AS-Wilson/RogueGP/Documentation/Porfolio/Renders/140720 2.jpg

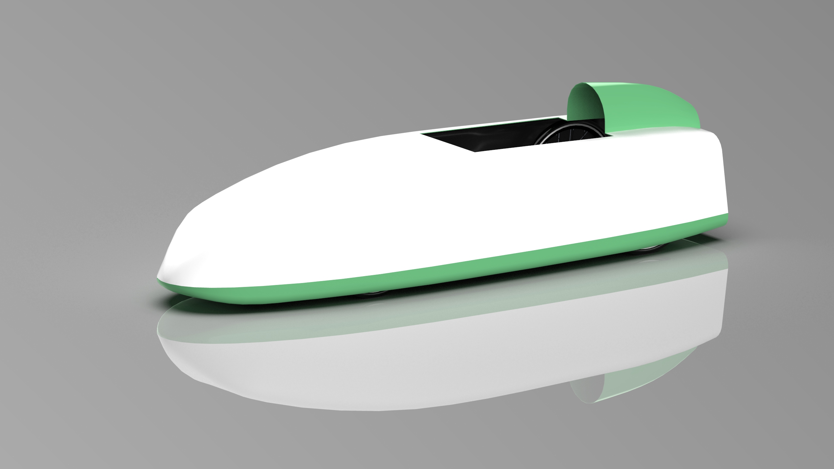
Documentation/Porfolio/Renders/140720 2.jpg
