AS-Wilson/RogueGP/Documentation/Porfolio/Renders/140720.jpg

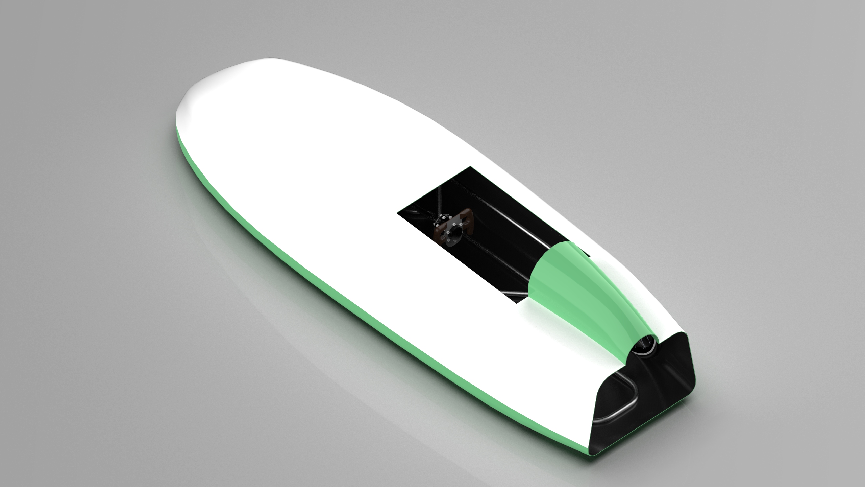
Documentation/Porfolio/Renders/140720.jpg
