AS-Wilson/RogueGP/Documentation/Porfolio/Renders/back.jpg

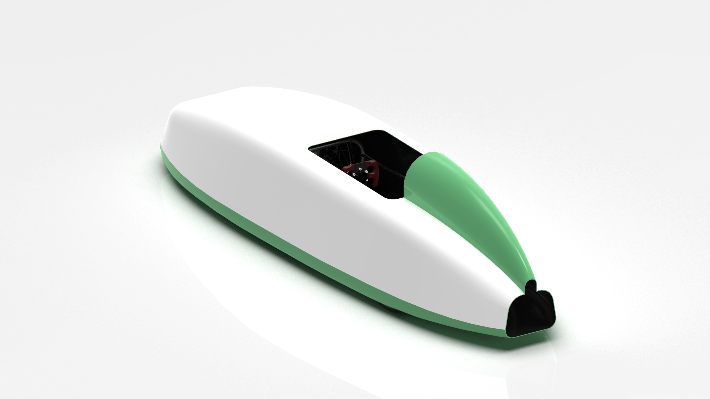
Documentation/Porfolio/Renders/back.jpg
