AS-Wilson/RogueGP/Documentation/Porfolio/Renders/Complete steering.jpg

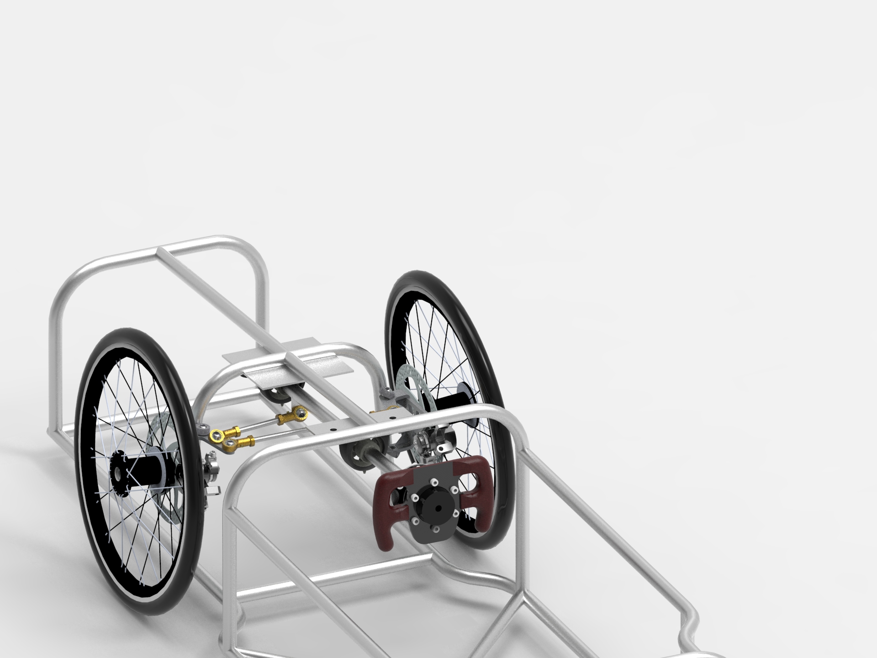
Documentation/Porfolio/Renders/Complete steering.jpg
