AS-Wilson/RogueGP/Documentation/Porfolio/Renders/Final Livery.jpg

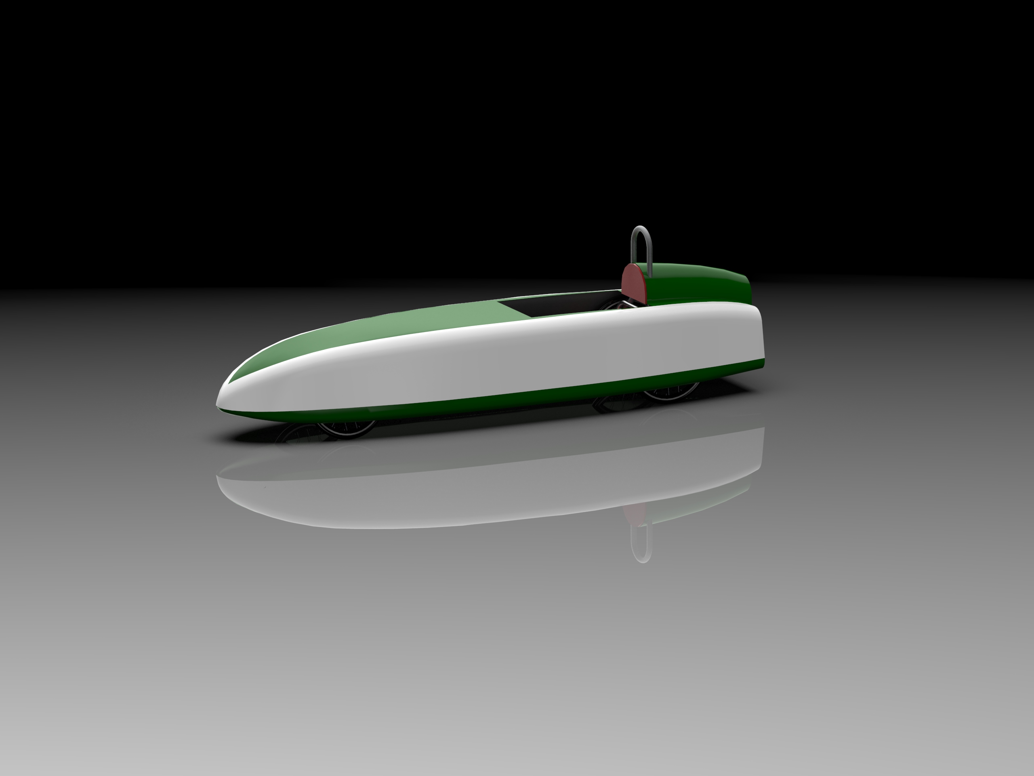
Documentation/Porfolio/Renders/Final Livery.jpg
