AS-Wilson/RogueGP/Documentation/Porfolio/Renders/front.jpg

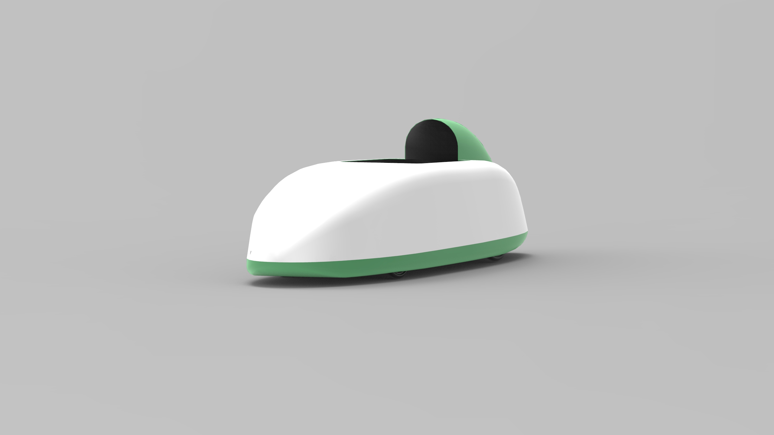
Documentation/Porfolio/Renders/front.jpg
