AS-Wilson/RogueGP/Documentation/Porfolio/Renders/Full Steering wheel 2.jpg

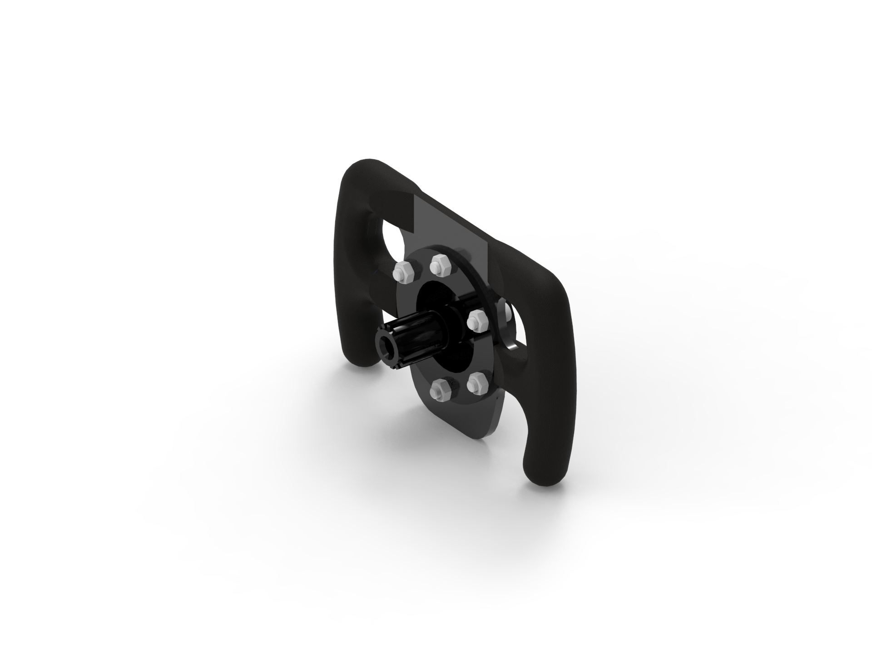
Documentation/Porfolio/Renders/Full Steering wheel 2.jpg
