AS-Wilson/RogueGP/Documentation/Porfolio/Renders/Full steering wheel.jpg

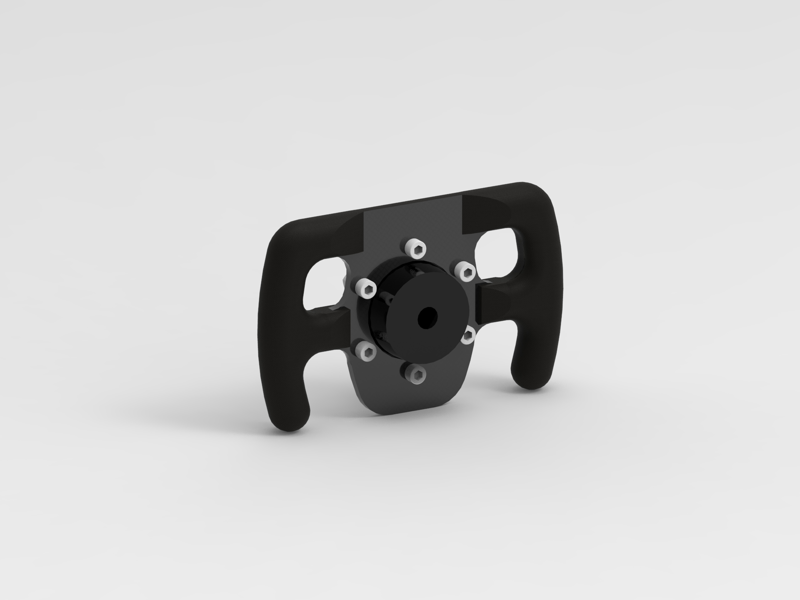
Documentation/Porfolio/Renders/Full steering wheel.jpg
