AS-Wilson/RogueGP/Documentation/Porfolio/Renders/KS®4539417097.115.jpg

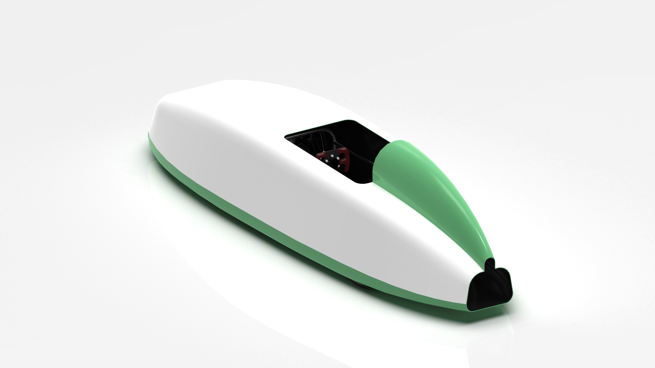
Documentation/Porfolio/Renders/KS®4539417097.115.jpg
