AS-Wilson/RogueGP/Documentation/Porfolio/Renders/Livery 1.jpg

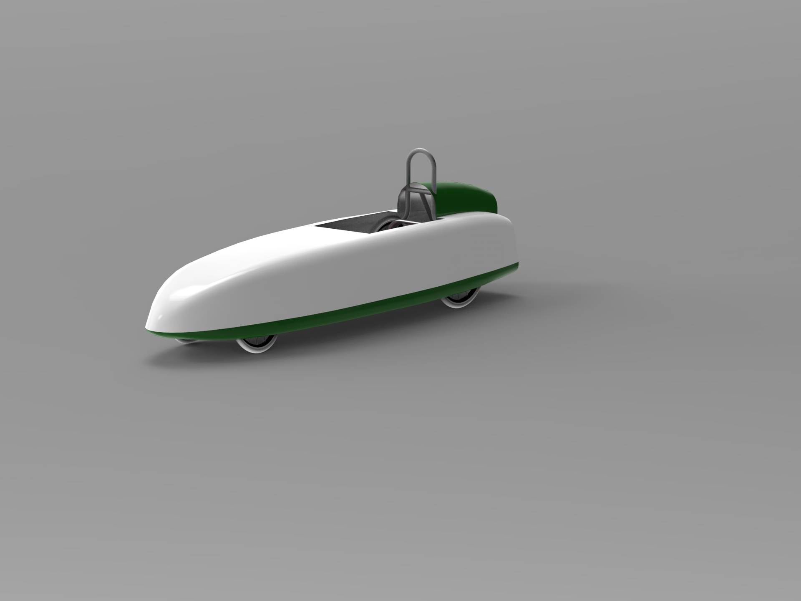
Documentation/Porfolio/Renders/Livery 1.jpg
