AS-Wilson/RogueGP/Documentation/Porfolio/Renders/Livery 1b.jpg

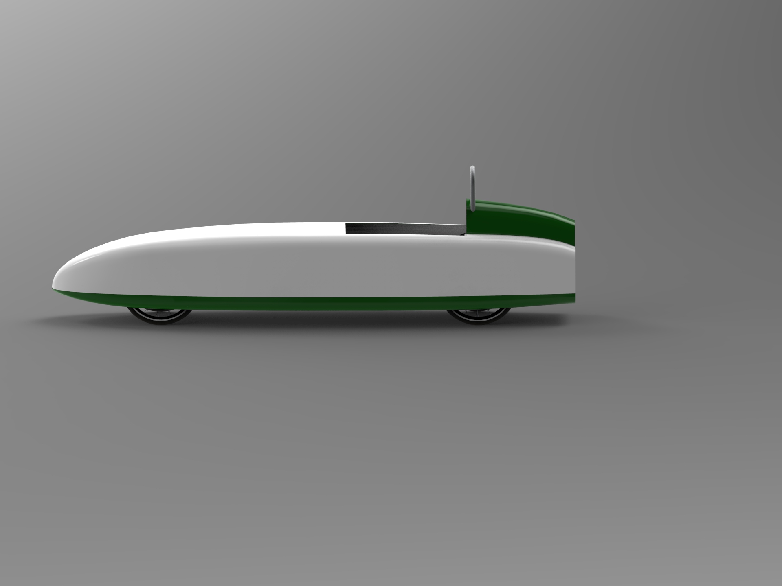
Documentation/Porfolio/Renders/Livery 1b.jpg
