AS-Wilson/RogueGP/Documentation/Porfolio/Renders/Livery 2.jpg

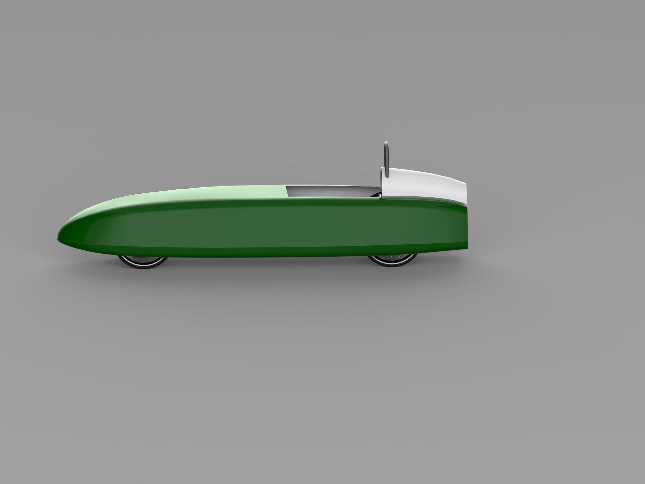
Documentation/Porfolio/Renders/Livery 2.jpg
