AS-Wilson/RogueGP/Documentation/Porfolio/Renders/Livery 3.jpg

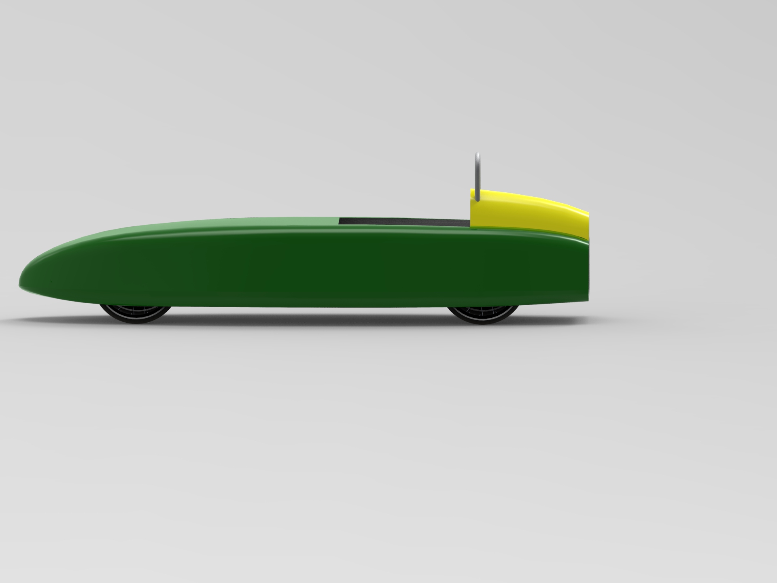
Documentation/Porfolio/Renders/Livery 3.jpg
