AS-Wilson/RogueGP/Documentation/Porfolio/Renders/Livery 4.jpg

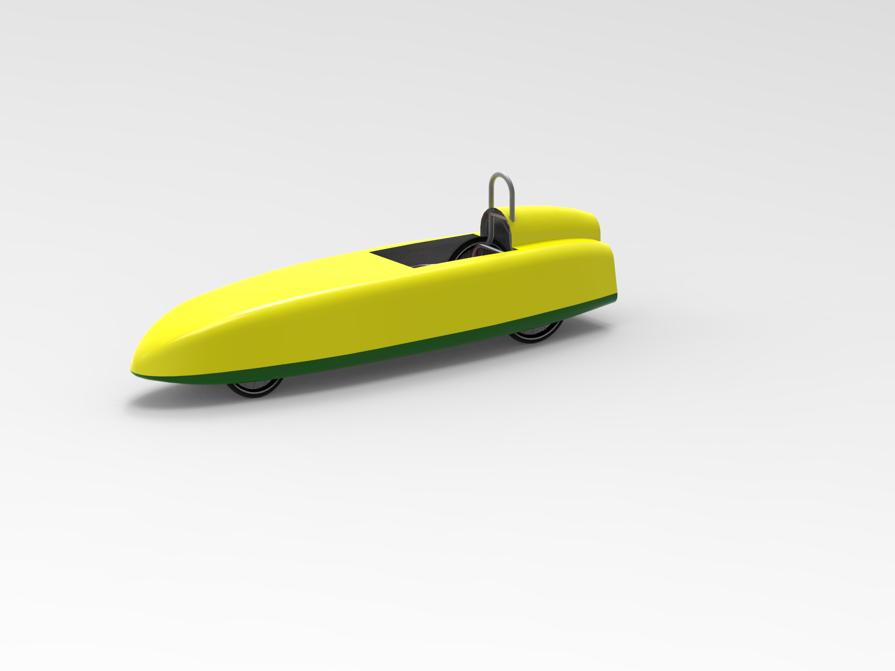
Documentation/Porfolio/Renders/Livery 4.jpg
