AS-Wilson/RogueGP/Documentation/Porfolio/Renders/Livery 5.jpg

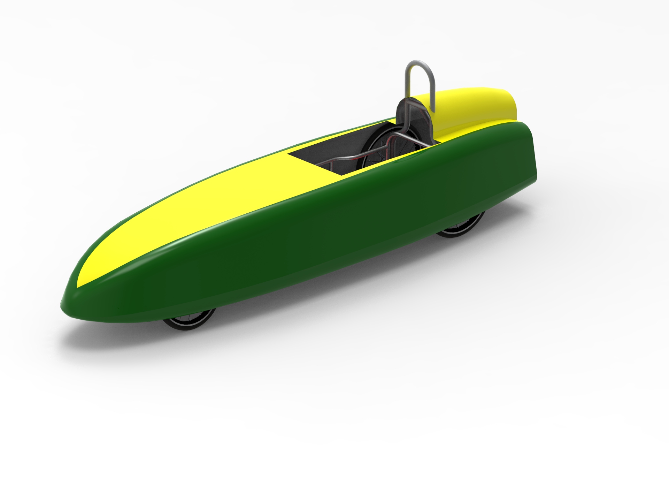
Documentation/Porfolio/Renders/Livery 5.jpg
