AS-Wilson/RogueGP/Documentation/Porfolio/Renders/Livery 6.jpg

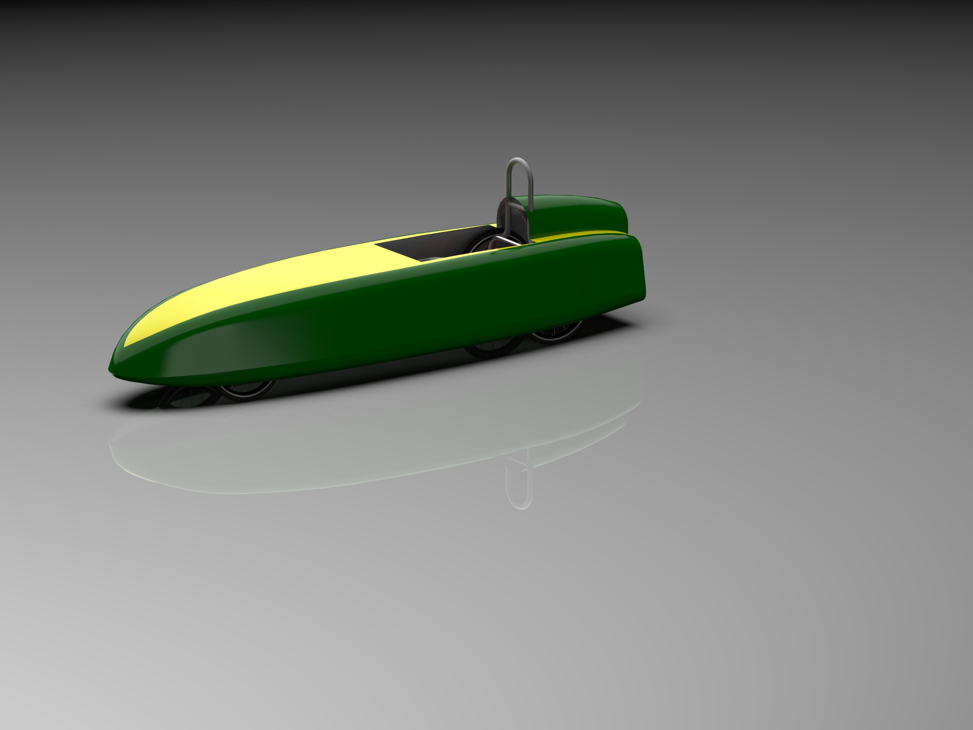
Documentation/Porfolio/Renders/Livery 6.jpg
