AS-Wilson/RogueGP/Documentation/Porfolio/Renders/Livery 7.jpg

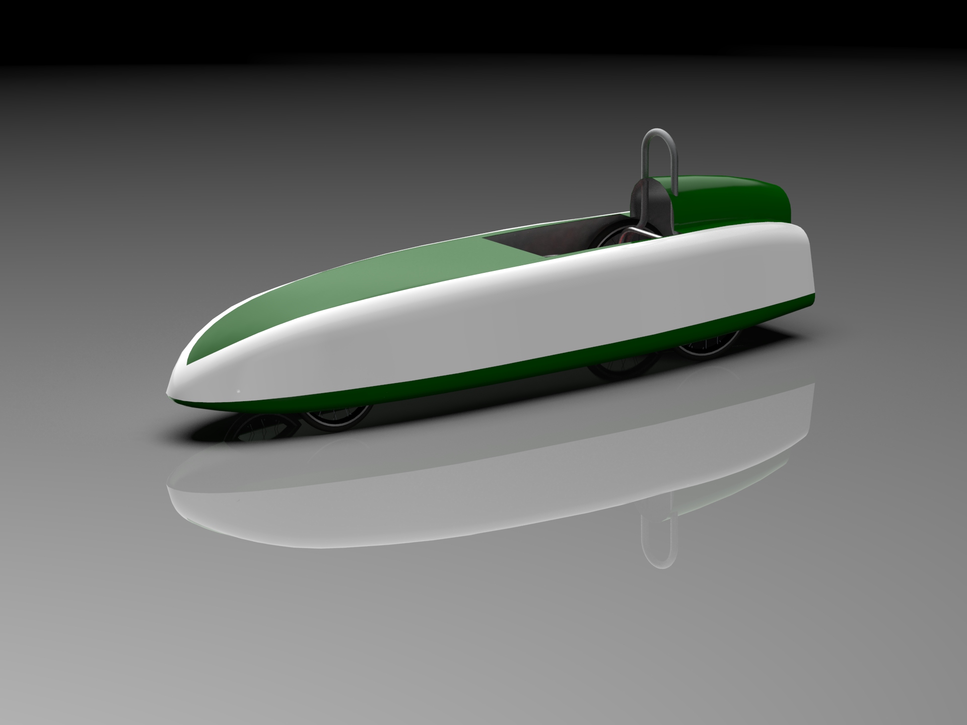
Documentation/Porfolio/Renders/Livery 7.jpg
