AS-Wilson/RogueGP/Documentation/Porfolio/Renders/Metallic white.jpg

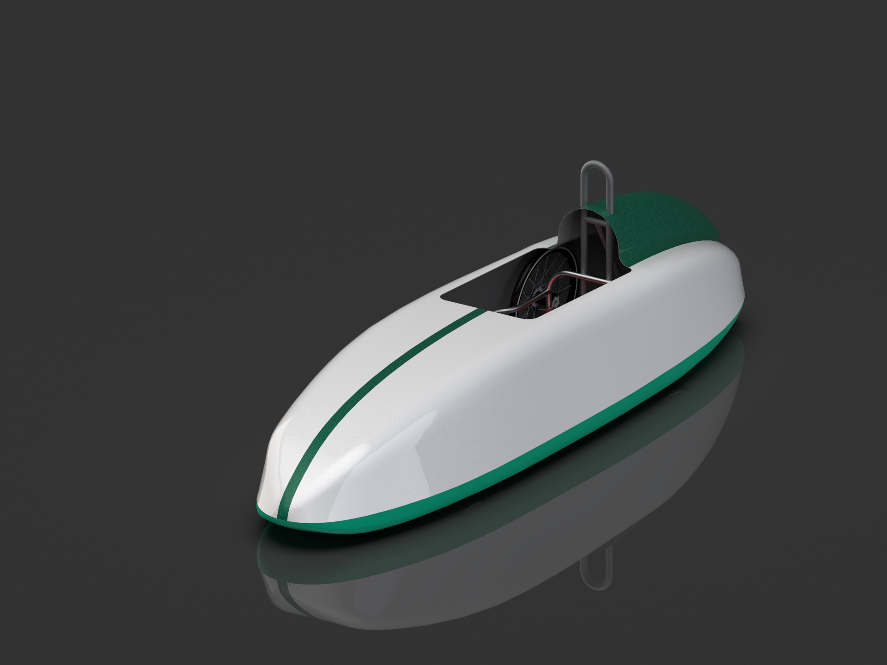
Documentation/Porfolio/Renders/Metallic white.jpg
