AS-Wilson/RogueGP/Documentation/Porfolio/Renders/Motor + batteries 1.jpg

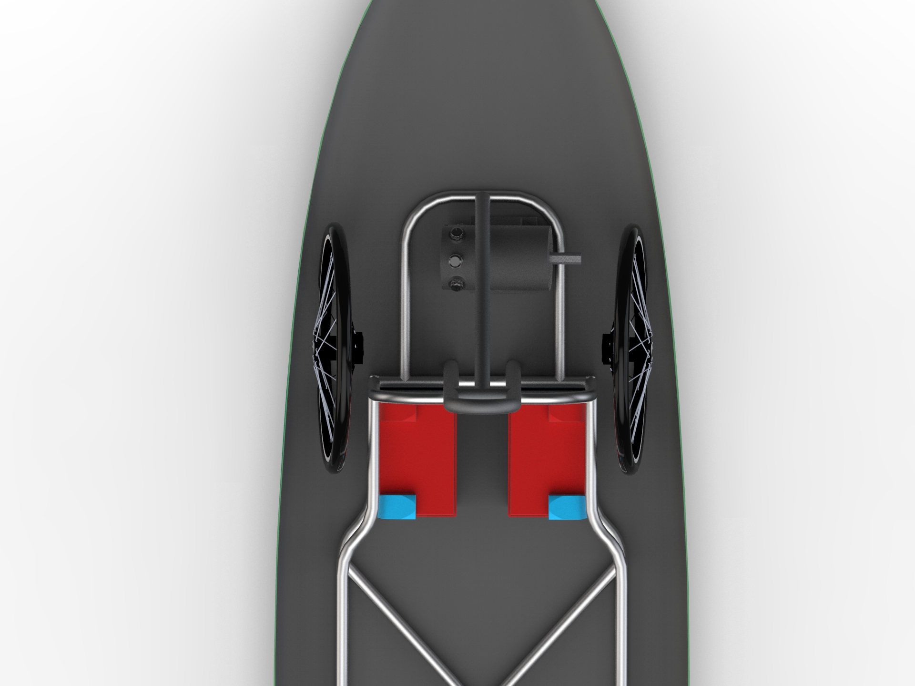
Documentation/Porfolio/Renders/Motor + batteries 1.jpg
