AS-Wilson/RogueGP/Documentation/Porfolio/Renders/Motor + batteries 2.jpg

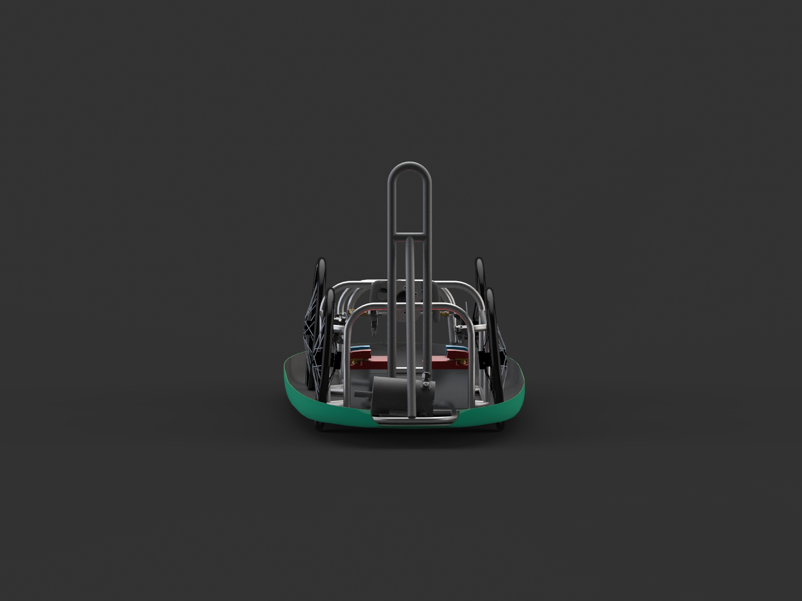
Documentation/Porfolio/Renders/Motor + batteries 2.jpg
