AS-Wilson/RogueGP/Documentation/Porfolio/Renders/Reworked MB1000.jpg

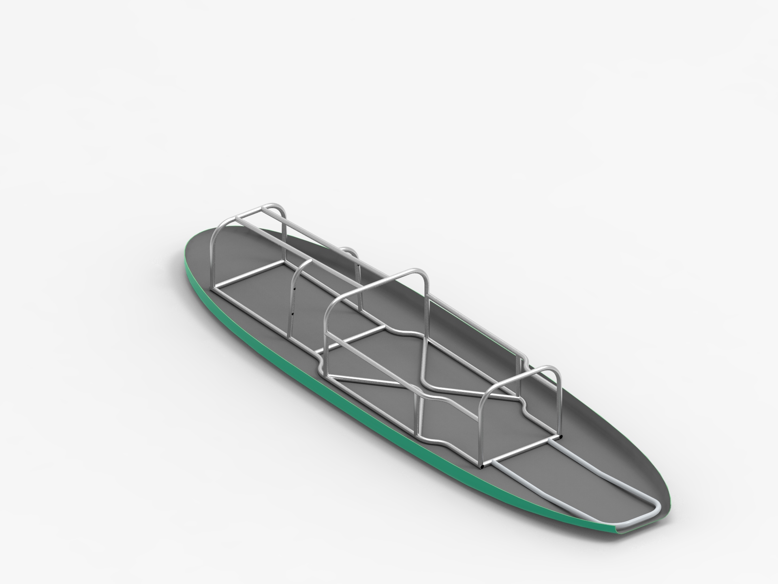
Documentation/Porfolio/Renders/Reworked MB1000.jpg
