AS-Wilson/RogueGP/Documentation/Porfolio/Renders/Right upright body 3mm.jpg

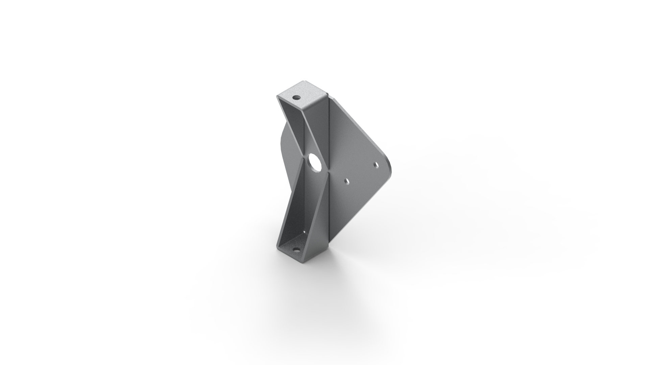
Documentation/Porfolio/Renders/Right upright body 3mm.jpg
