AS-Wilson/RogueGP/Documentation/Porfolio/Renders/Right upright body v2.jpg

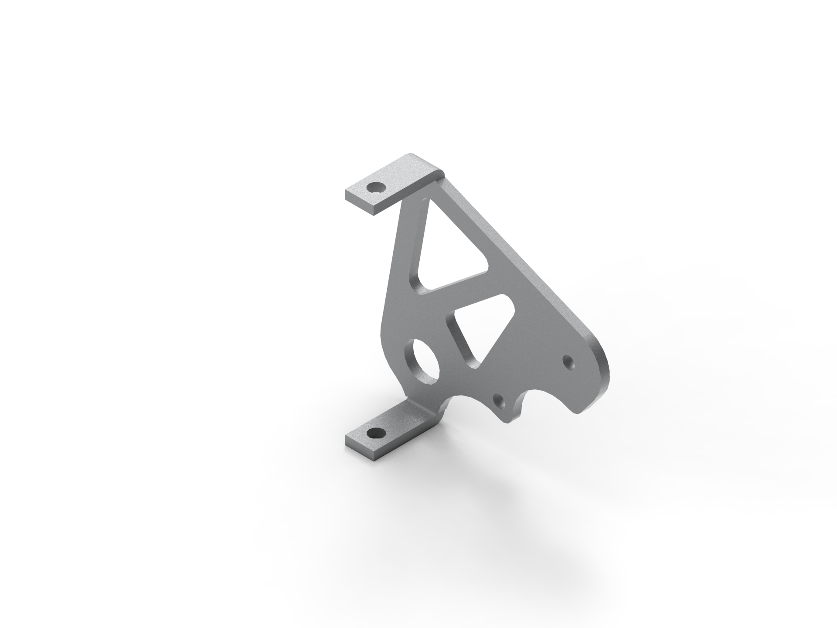
Documentation/Porfolio/Renders/Right upright body v2.jpg
