AS-Wilson/RogueGP/Documentation/Porfolio/Renders/Right Upright.jpg

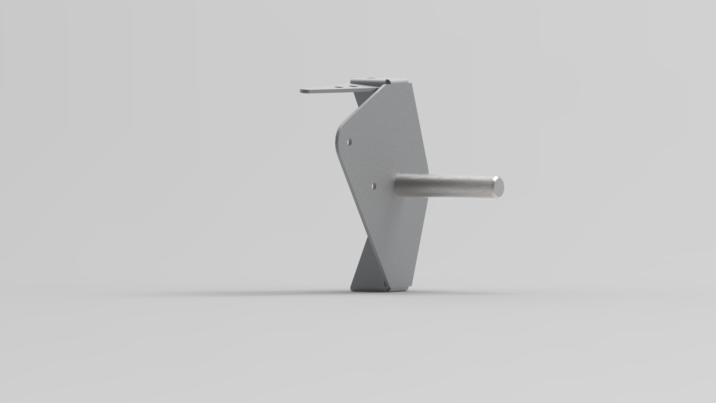
Documentation/Porfolio/Renders/Right Upright.jpg
