AS-Wilson/RogueGP/Documentation/Porfolio/Renders/Side final fairing.jpg

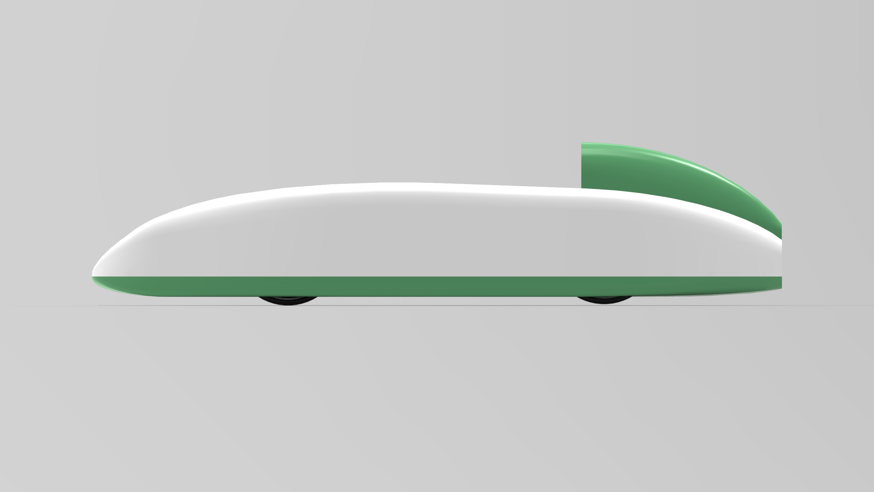
Documentation/Porfolio/Renders/Side final fairing.jpg
