AS-Wilson/RogueGP/Electrical&Electronic/Controler Spec.PNG

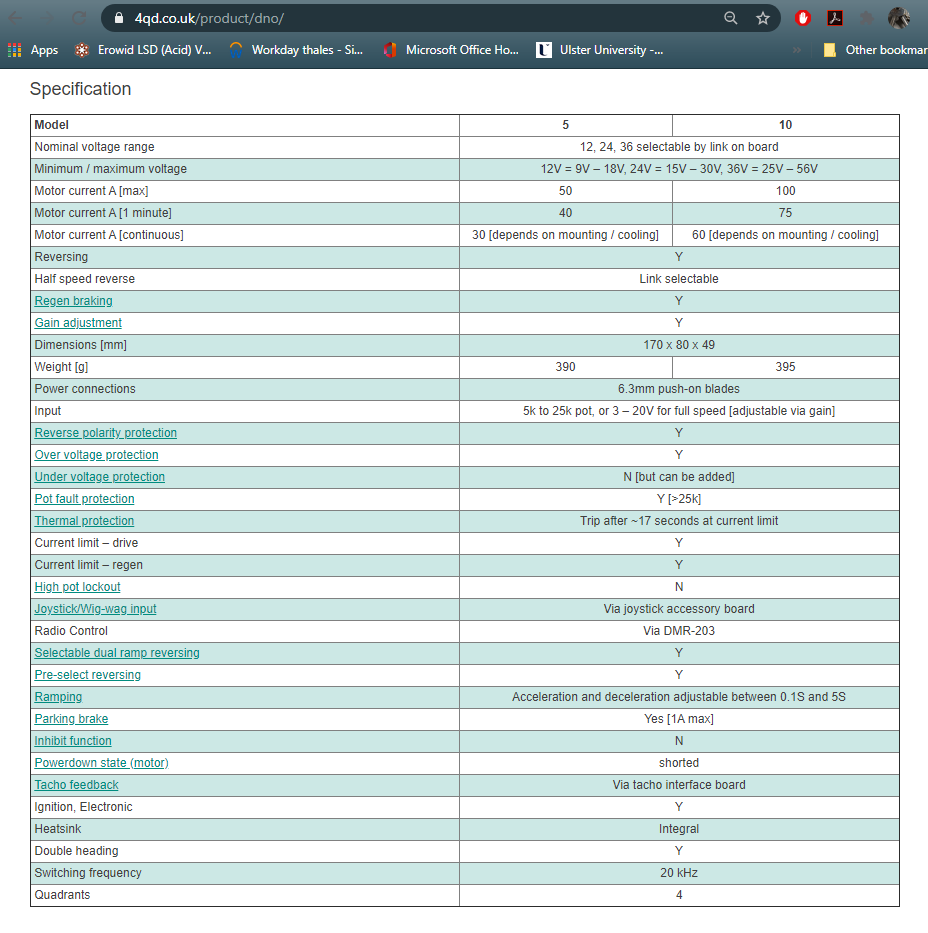
Electrical&Electronic/Controler Spec.PNG
