AS-Wilson/RogueGP/Mechanical/drivetrain/CVT/example-CVT/cinghia/belt.JPG

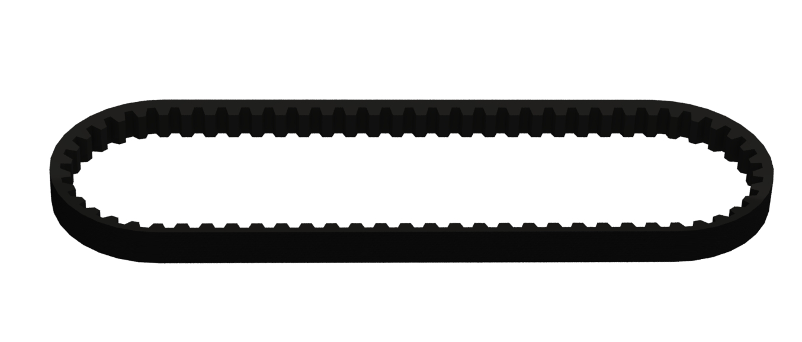
Mechanical/drivetrain/CVT/example-CVT/cinghia/belt.JPG
