AS-Wilson/RogueGP/Mechanical/drivetrain/CVT/example-CVT/Clutch-Bell/preview2.JPG

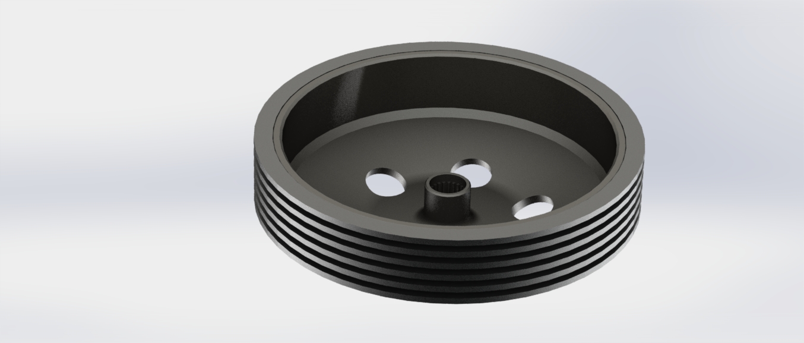
Mechanical/drivetrain/CVT/example-CVT/Clutch-Bell/preview2.JPG
