AS-Wilson/RogueGP/Mechanical/drivetrain/CVT/example-CVT/Clutch-Bell/preview.JPG

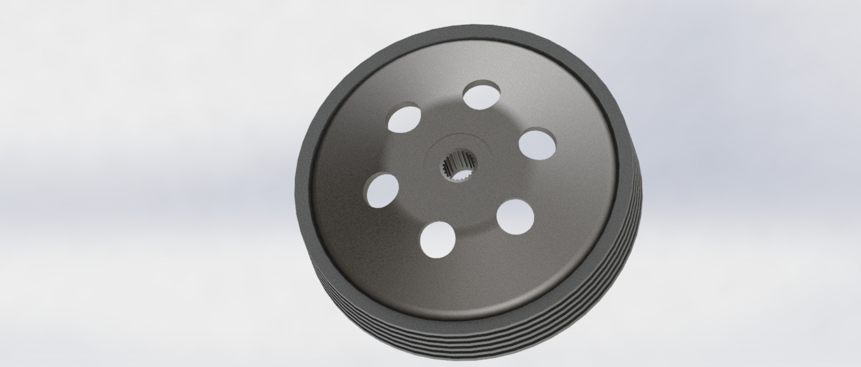
Mechanical/drivetrain/CVT/example-CVT/Clutch-Bell/preview.JPG
