AS-Wilson/RogueGP/Mechanical/drivetrain/CVT/example-CVT/Clutch/render1.JPG

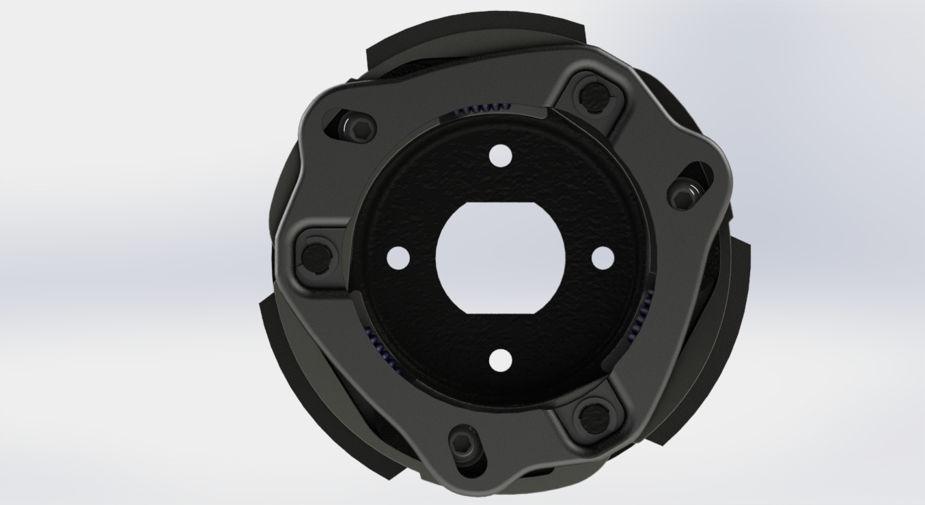
Mechanical/drivetrain/CVT/example-CVT/Clutch/render1.JPG
