AS-Wilson/RogueGP/Mechanical/drivetrain/CVT/example-CVT/Clutch/render2.JPG

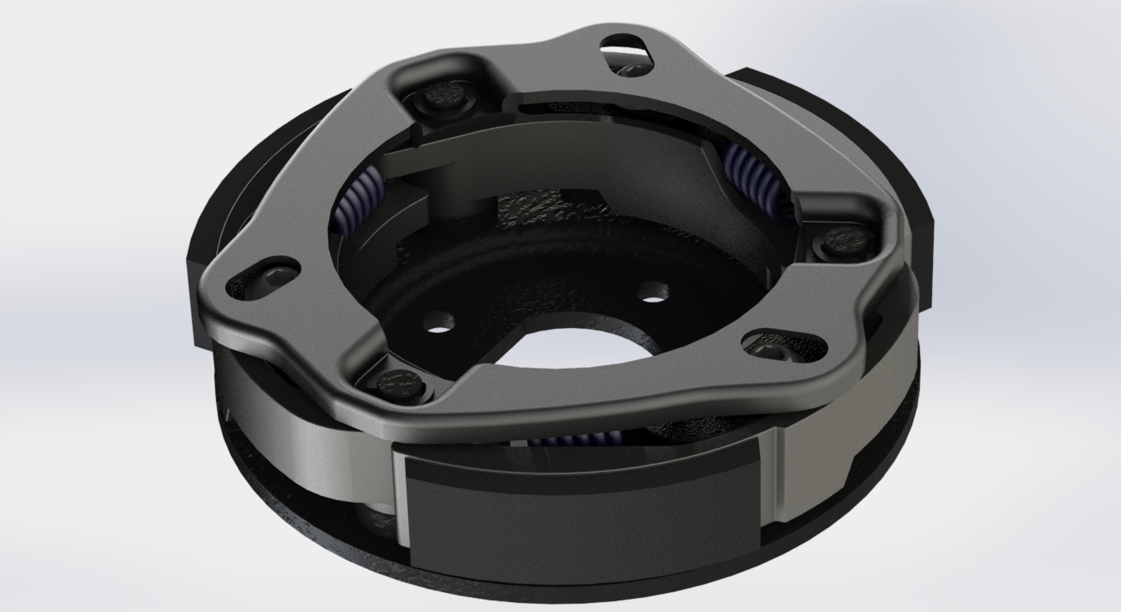
Mechanical/drivetrain/CVT/example-CVT/Clutch/render2.JPG
