AS-Wilson/RogueGP/Mechanical/drivetrain/CVT/example-CVT/Clutch/render3.JPG

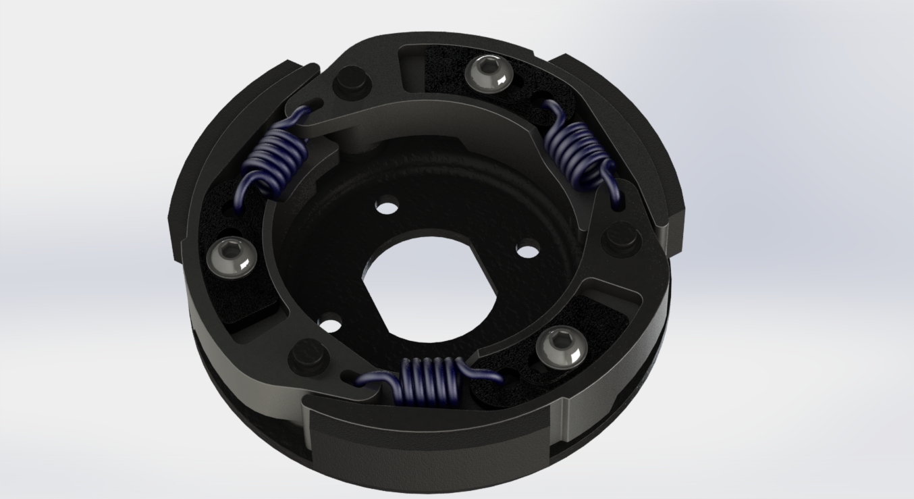
Mechanical/drivetrain/CVT/example-CVT/Clutch/render3.JPG
