AS-Wilson/RogueGP/Mechanical/drivetrain/CVT/example-CVT/Clutch/render5.JPG

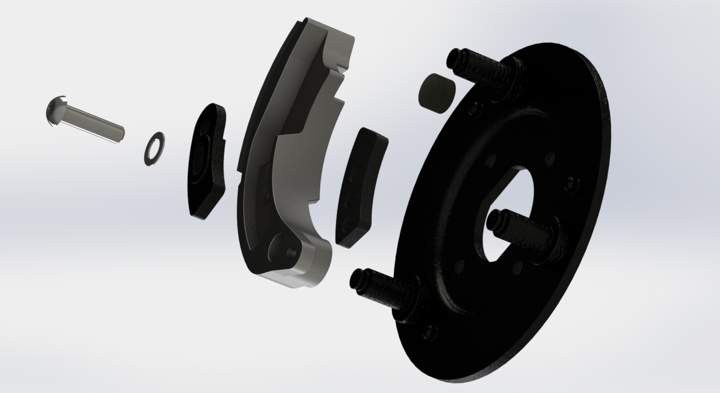
Mechanical/drivetrain/CVT/example-CVT/Clutch/render5.JPG
