AS-Wilson/RogueGP/Mechanical/drivetrain/CVT/example-CVT/CVT/Untitled3.JPG

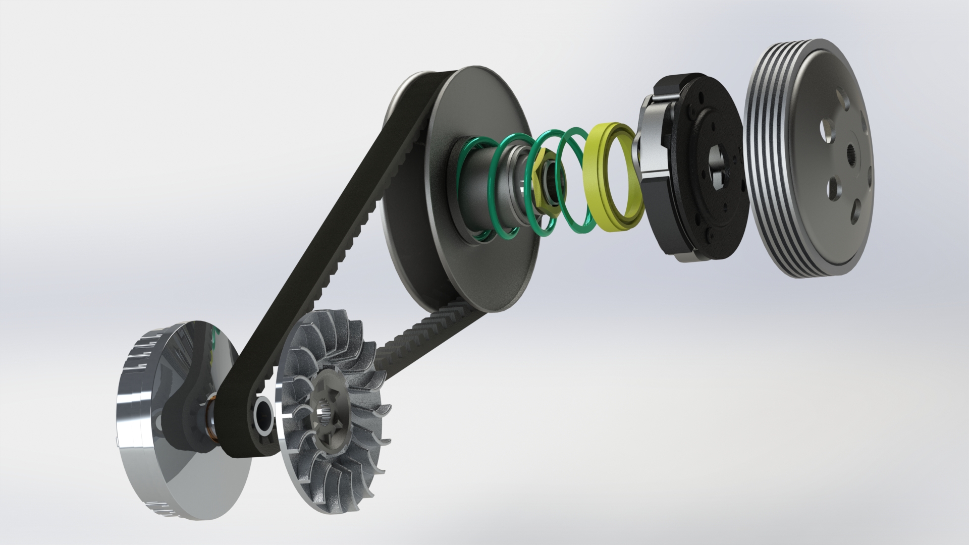
Mechanical/drivetrain/CVT/example-CVT/CVT/Untitled3.JPG
