AS-Wilson/RogueGP/Mechanical/drivetrain/CVT/example-CVT/CVT/Untitled4.JPG

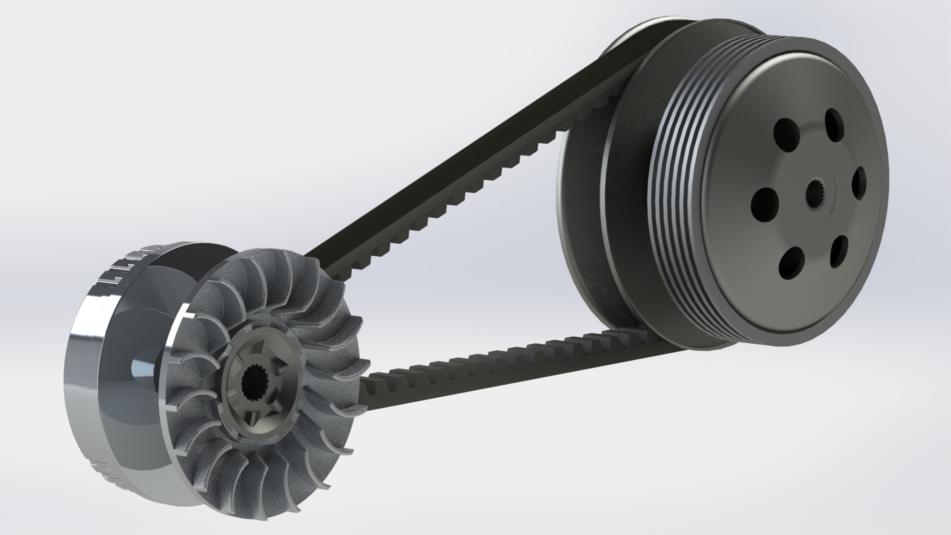
Mechanical/drivetrain/CVT/example-CVT/CVT/Untitled4.JPG
