AS-Wilson/RogueGP/Mechanical/drivetrain/CVT/example-CVT/Torque-Driver/preview2.JPG

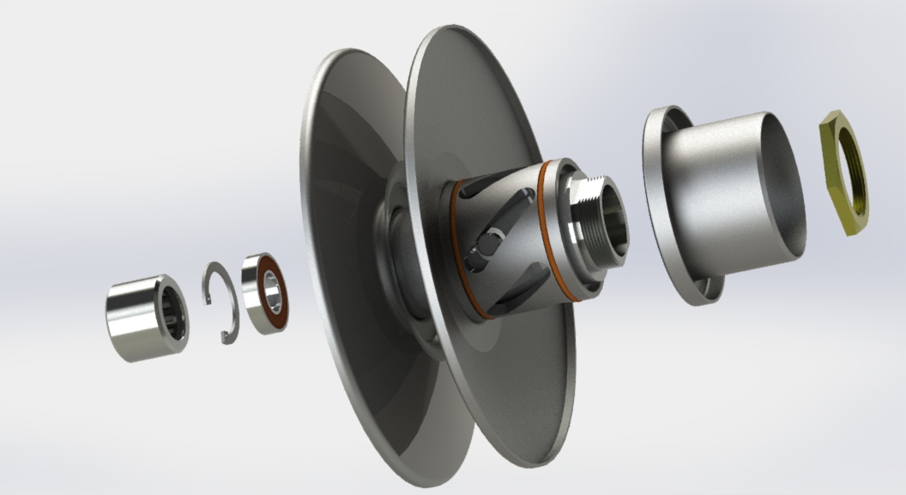
Mechanical/drivetrain/CVT/example-CVT/Torque-Driver/preview2.JPG
