AS-Wilson/RogueGP/Mechanical/drivetrain/CVT/example-CVT/Torque-Driver/preview3.JPG

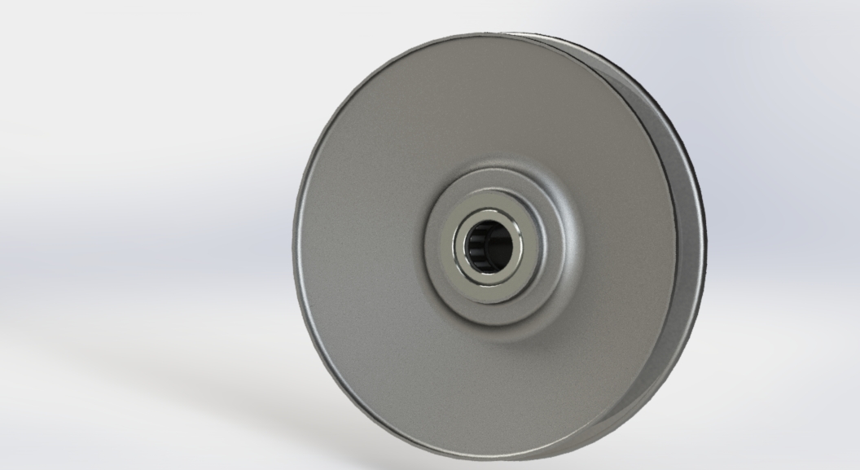
Mechanical/drivetrain/CVT/example-CVT/Torque-Driver/preview3.JPG
