AS-Wilson/RogueGP/Mechanical/drivetrain/CVT/example-CVT/Variator-multivar2000/preview3.JPG

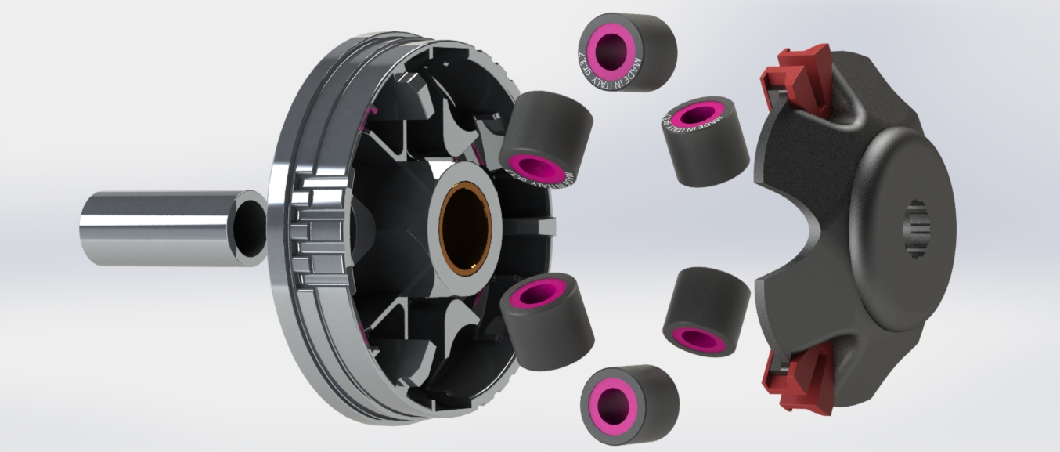
Mechanical/drivetrain/CVT/example-CVT/Variator-multivar2000/preview3.JPG
