AS-Wilson/RogueGP/Mechanical/drivetrain/CVT/example-CVT/Variator-multivar2000/Untitled-2.png

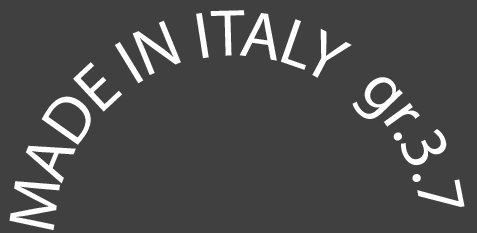
Mechanical/drivetrain/CVT/example-CVT/Variator-multivar2000/Untitled-2.png
