AS-Wilson/RogueGP/Mechanical/drivetrain/CVT/example-CVT/ventilvar/preview.JPG

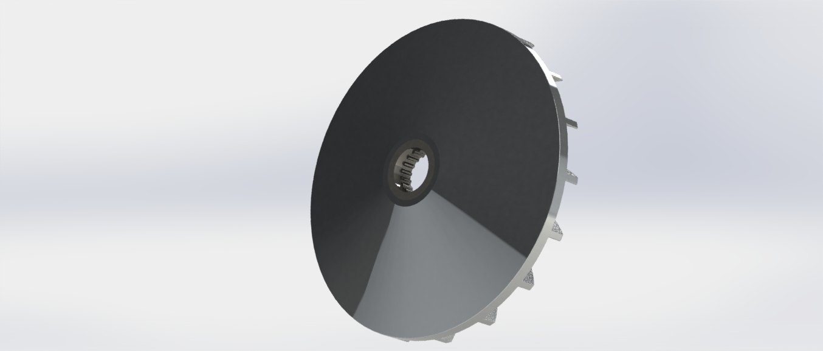
Mechanical/drivetrain/CVT/example-CVT/ventilvar/preview.JPG
