AS-Wilson/RogueGP/Documentation/Part Drawings & Exports/Exports/LH-axle.stp

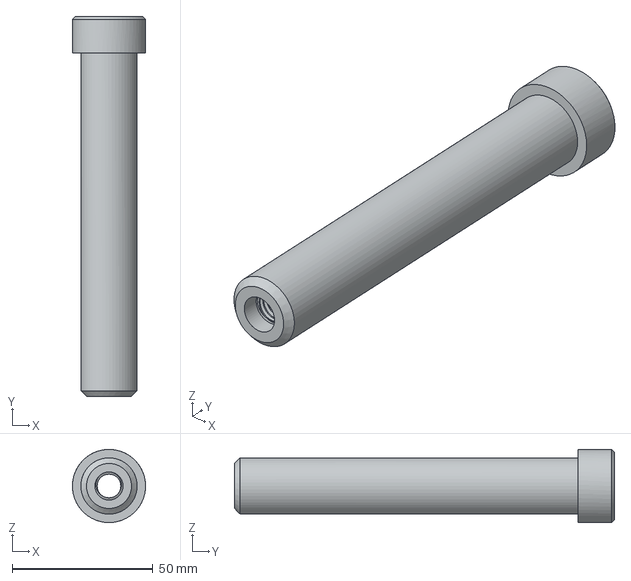
[picture p73: CAD file, 2020-09-22]
Documentation/Part Drawings & Exports/Exports/LH-axle.stp
26.0 x 135.0 x 26.0 mm
