AS-Wilson/RogueGP/Mechanical/drivetrain/CVT/example-CVT/carter/supporto.SLDPRT

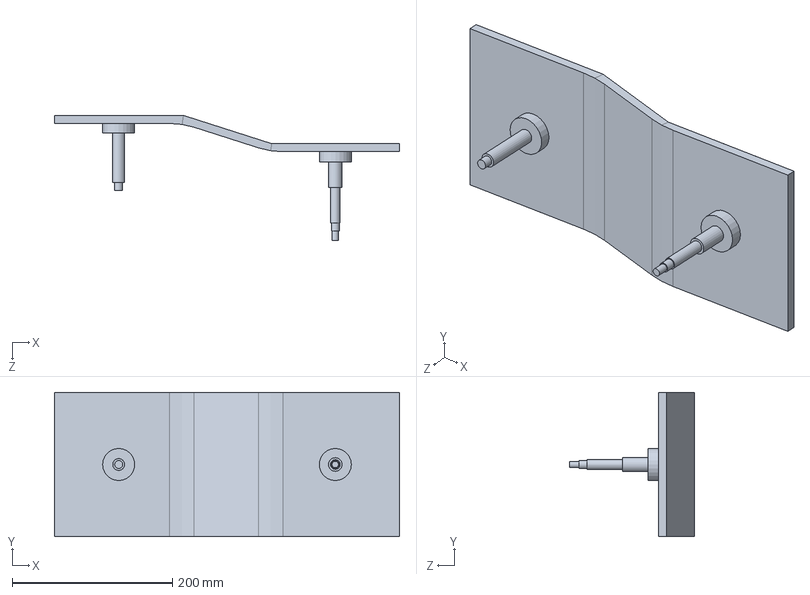
[picture p74: CAD file, 2020-09-12]
Mechanical/drivetrain/CVT/example-CVT/carter/supporto.SLDPRT
430.0 x 180.0 x 156.0 mm
