AS-Wilson/RogueGP/Mechanical/drivetrain/CVT/example-CVT/cinghia/dente.SLDPRT

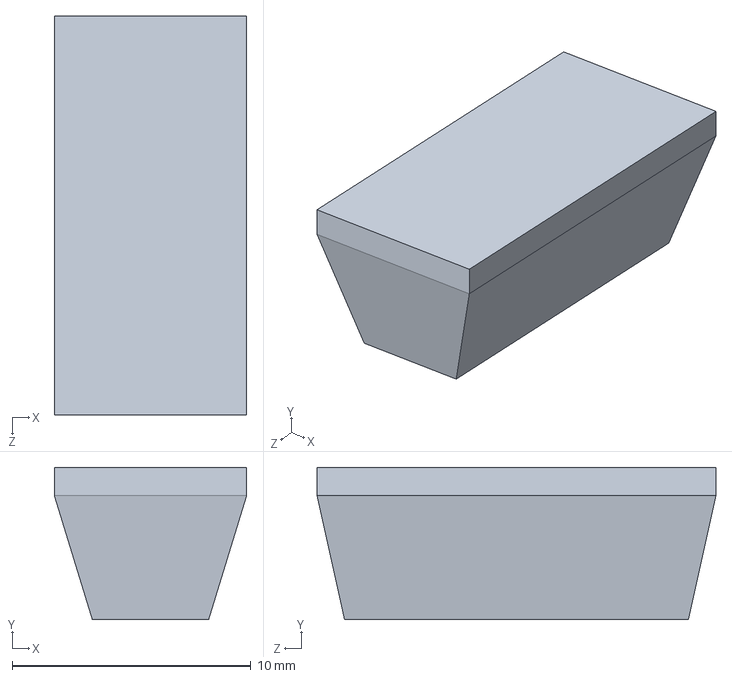
[picture p75: CAD file, 2020-09-12]
Mechanical/drivetrain/CVT/example-CVT/cinghia/dente.SLDPRT
8.06 x 6.38 x 16.7 mm
