AS-Wilson/RogueGP/Mechanical/drivetrain/CVT/example-CVT/Clutch-Bell/CLBPart1.SLDPRT

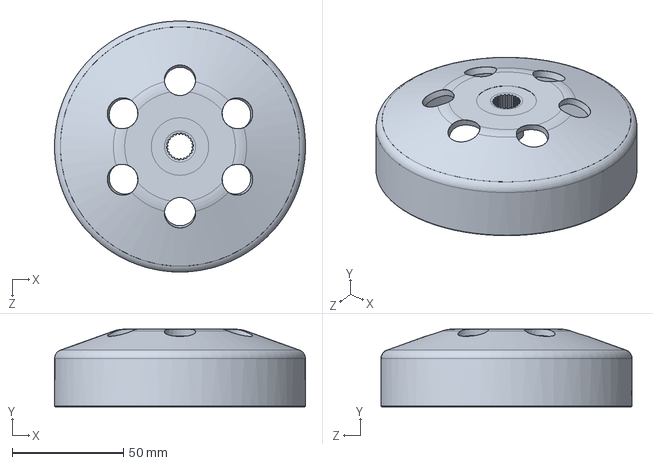
[picture p76: CAD file, 2020-09-12]
Mechanical/drivetrain/CVT/example-CVT/Clutch-Bell/CLBPart1.SLDPRT
113.0 x 35.0 x 113.0 mm
