AS-Wilson/RogueGP/Mechanical/drivetrain/CVT/example-CVT/Clutch/CLPart3.SLDPRT

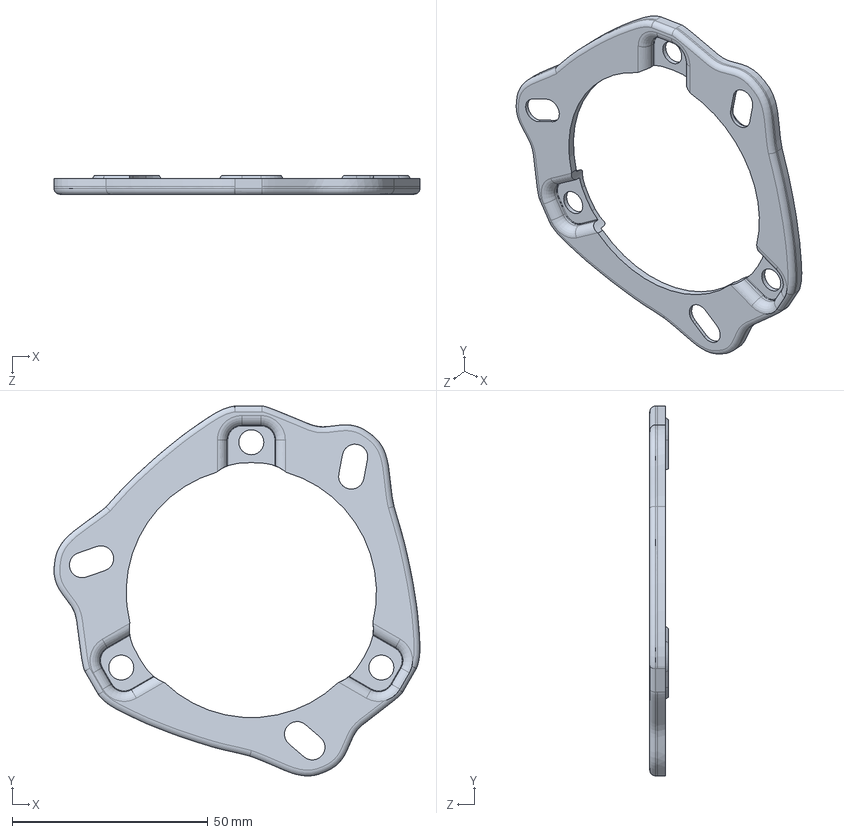
[picture p77: CAD file, 2020-09-12]
Mechanical/drivetrain/CVT/example-CVT/Clutch/CLPart3.SLDPRT
93.6 x 94.6 x 4.75 mm
