AS-Wilson/RogueGP/Mechanical/drivetrain/CVT/example-CVT/MdC/MdC2.SLDPRT

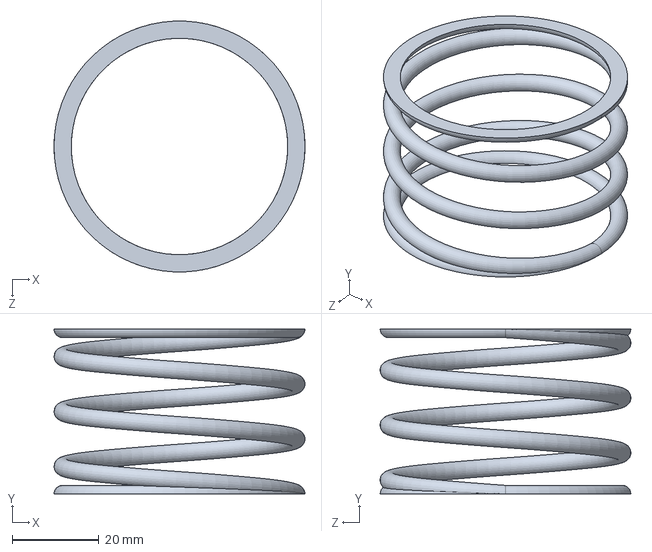
[picture p78: CAD file, 2020-09-12]
Mechanical/drivetrain/CVT/example-CVT/MdC/MdC2.SLDPRT
58.0 x 38.1 x 58.0 mm
