AS-Wilson/RogueGP/Mechanical/drivetrain/CVT/example-CVT/Torque-Driver/Parte6.SLDPRT

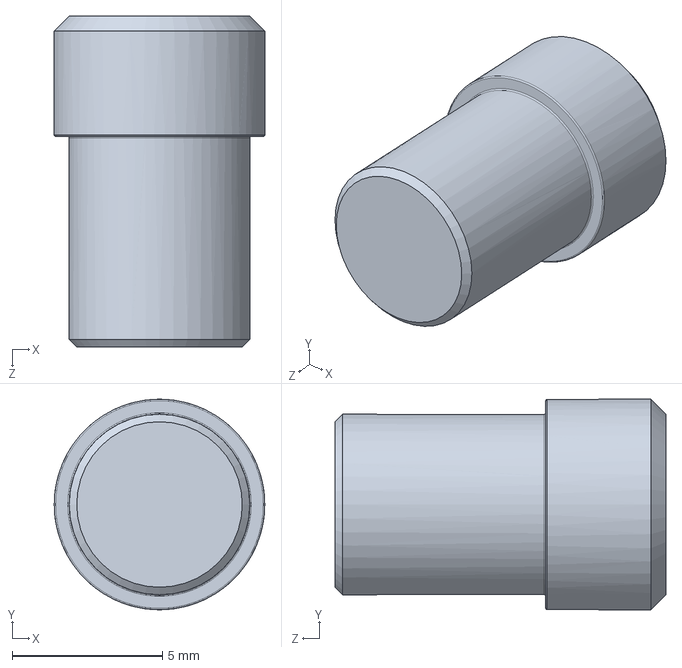
[picture p79: CAD file, 2020-09-12]
Mechanical/drivetrain/CVT/example-CVT/Torque-Driver/Parte6.SLDPRT
7.00 x 7.00 x 11.0 mm
