AS-Wilson/RogueGP/Mechanical/drivetrain/CVT/example-CVT/Variator-multivar2000/roller weight.SLDPRT

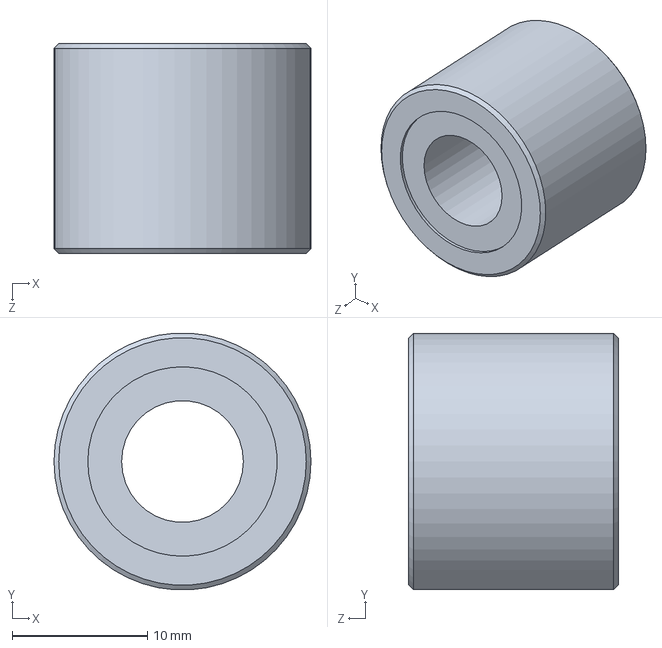
[picture p80: CAD file, 2020-09-12]
Mechanical/drivetrain/CVT/example-CVT/Variator-multivar2000/roller weight.SLDPRT
19.0 x 19.0 x 15.5 mm
