AS-Wilson/RogueGP/Mechanical/drivetrain/CVT/example-CVT/ventilvar/VENParte4.SLDPRT

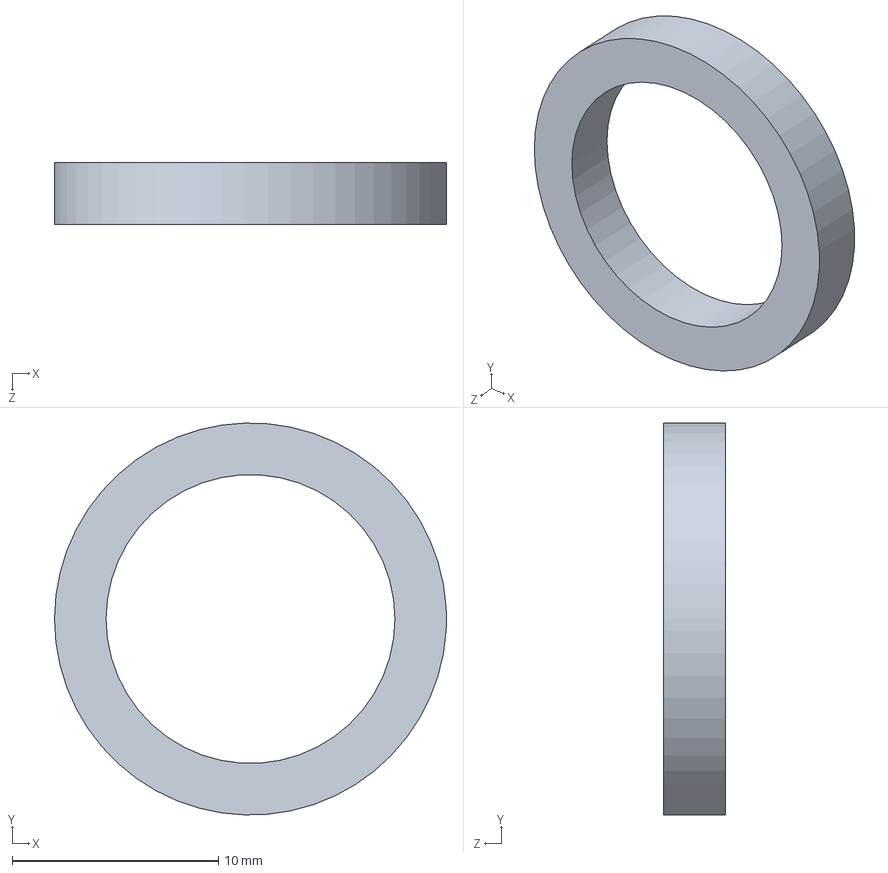
[picture p81: CAD file, 2020-09-12]
Mechanical/drivetrain/CVT/example-CVT/ventilvar/VENParte4.SLDPRT
19.0 x 19.0 x 3.00 mm
