AS-Wilson/RogueGP/Mechanical/MB1000-Chassis/battery-holder/battery-tray-flat.dxf

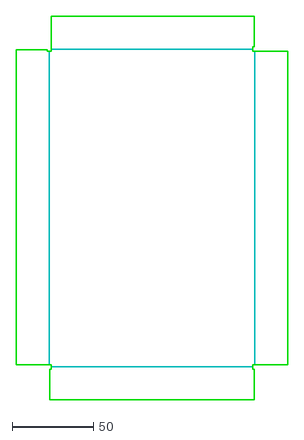
[picture p82: CAD file, 2020-09-09]
Mechanical/MB1000-Chassis/battery-holder/battery-tray-flat.dxf
167.2 x 236.2
