AS-Wilson/RogueGP/Mechanical/rolling-shell/pillow-bearing-TUCP204.step

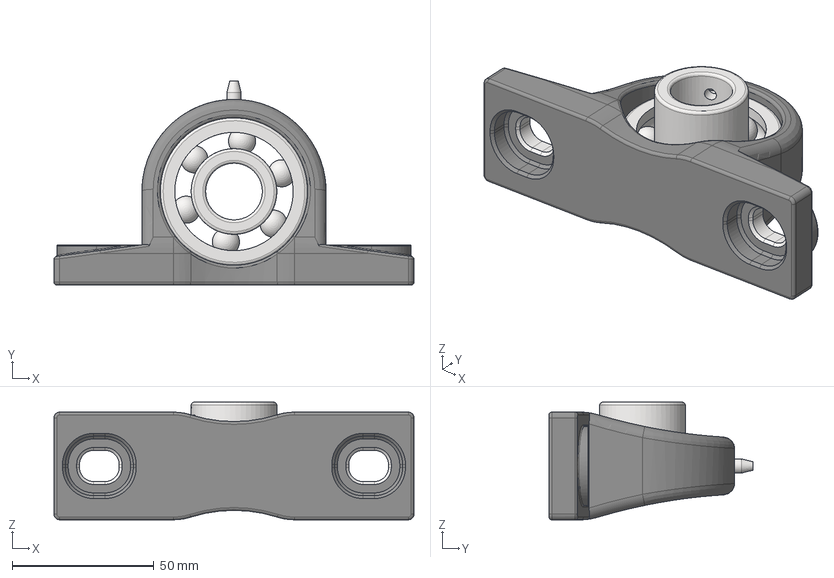
[picture p83: CAD file, 2020-09-09]
Mechanical/rolling-shell/pillow-bearing-TUCP204.step
127.0 x 72.0 x 41.5 mm
Gehaeuse
DIN 625 SKF- beidseitig abgedichtet SKF 6304-2RS1
