AS-Wilson/RogueGP/Mechanical/standard-parts-&-example-designs/example-CVT/cinghia/extbelt.SLDPRT

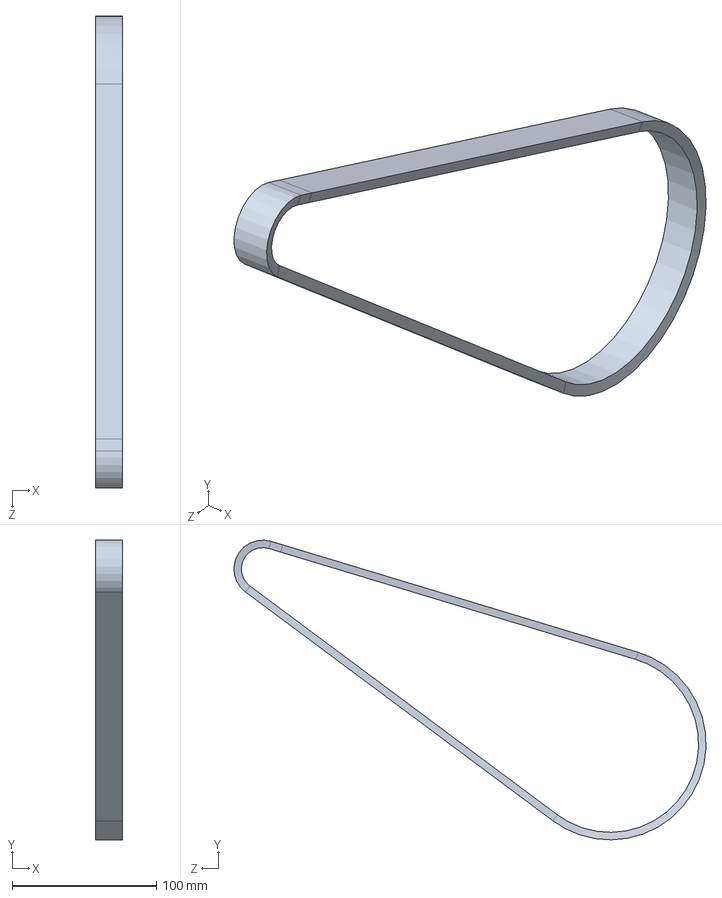
[picture p84: CAD file, 2020-09-12]
Mechanical/standard-parts-&-example-designs/example-CVT/cinghia/extbelt.SLDPRT
19.0 x 208.0 x 327.5 mm
