AS-Wilson/RogueGP/Mechanical/standard-parts-&-example-designs/example-CVT/Clutch/CLpart8.SLDPRT

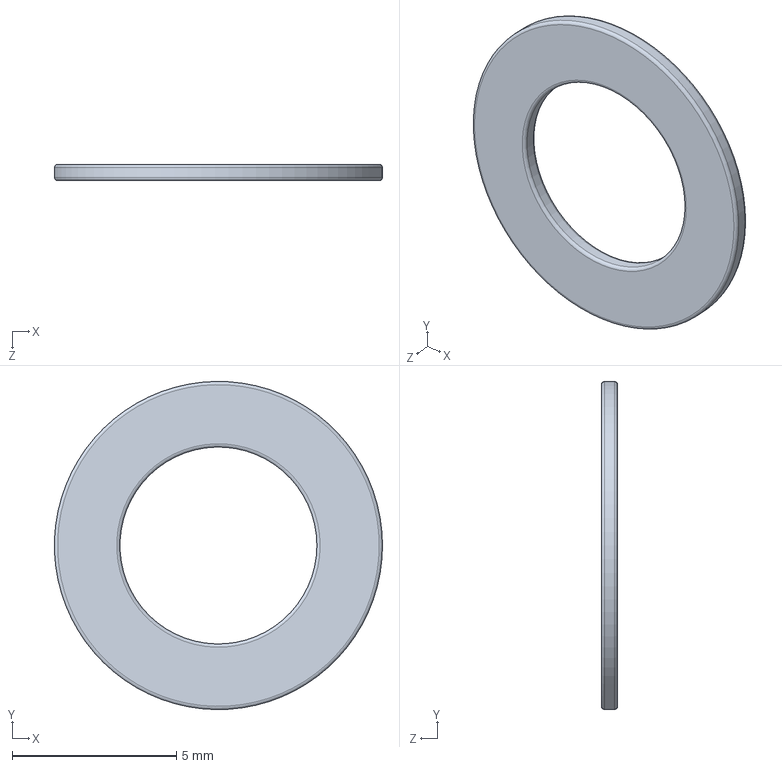
[picture p85: CAD file, 2020-09-12]
Mechanical/standard-parts-&-example-designs/example-CVT/Clutch/CLpart8.SLDPRT
10.00 x 10.00 x 0.5 mm
