AS-Wilson/RogueGP/Mechanical/standard-parts-&-example-designs/example-CVT/Torque-Driver/TQParte5.SLDPRT

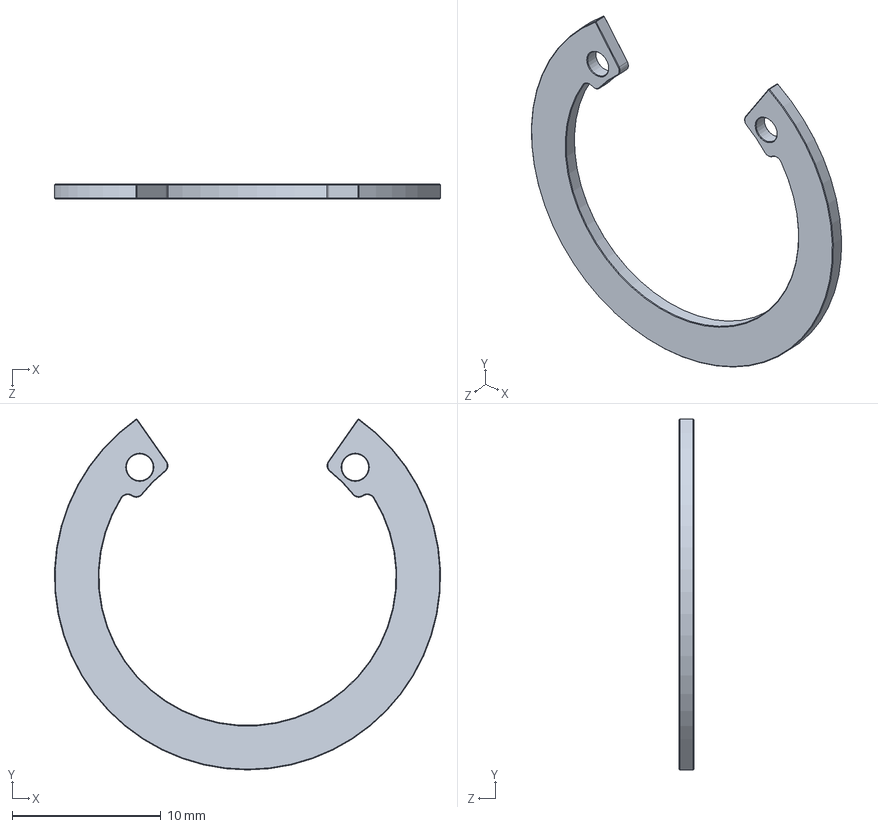
[picture p86: CAD file, 2020-09-12]
Mechanical/standard-parts-&-example-designs/example-CVT/Torque-Driver/TQParte5.SLDPRT
26.0 x 23.6 x 1.00 mm
