AS-Wilson/RogueGP/Mechanical/standard-parts-&-example-designs/example-CVT/ventilvar/VENParte5.SLDPRT

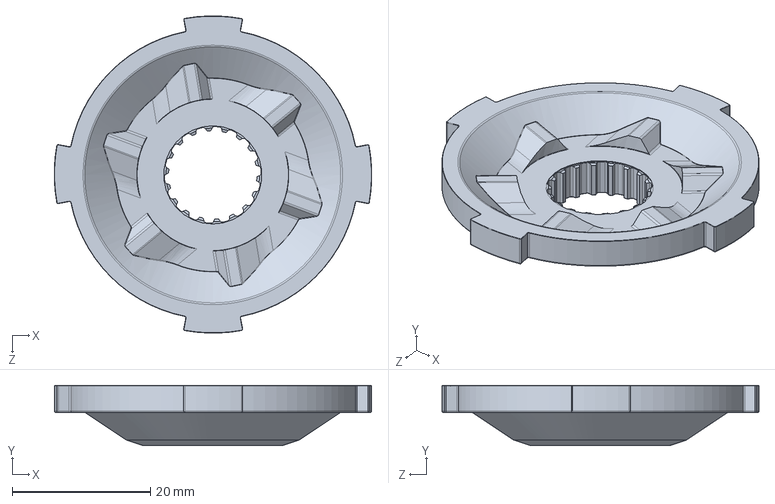
[picture p87: CAD file, 2020-09-12]
Mechanical/standard-parts-&-example-designs/example-CVT/ventilvar/VENParte5.SLDPRT
45.9 x 8.69 x 45.9 mm
