AS-Wilson/RogueGP/Mechanical/Suspension-&-Steering/Uprights/Exports/front-axle/front-axle.stp

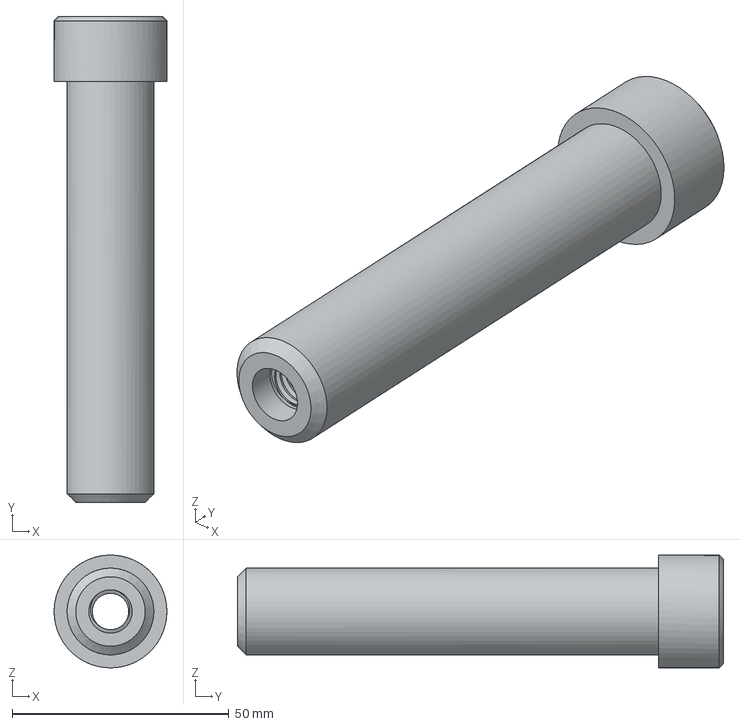
[picture p88: CAD file, 2020-08-05]
Mechanical/Suspension-&-Steering/Uprights/Exports/front-axle/front-axle.stp
26.0 x 112.0 x 26.0 mm
