AS-Wilson/RogueGP/Documentation/Part Drawings & Exports/Exports/2020-heat-sink.stp

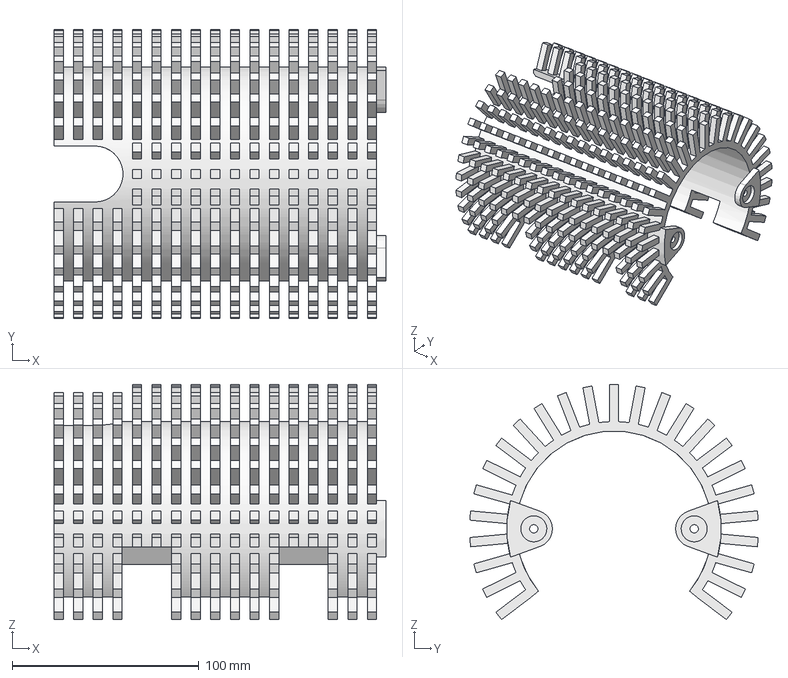
[picture p89: CAD file, 2020-09-22]
Documentation/Part Drawings & Exports/Exports/2020-heat-sink.stp
178.0 x 154.7 x 126.1 mm
