AS-Wilson/RogueGP/Mechanical/drivetrain/CVT/example-CVT/cinghia/cinghia.SLDPRT

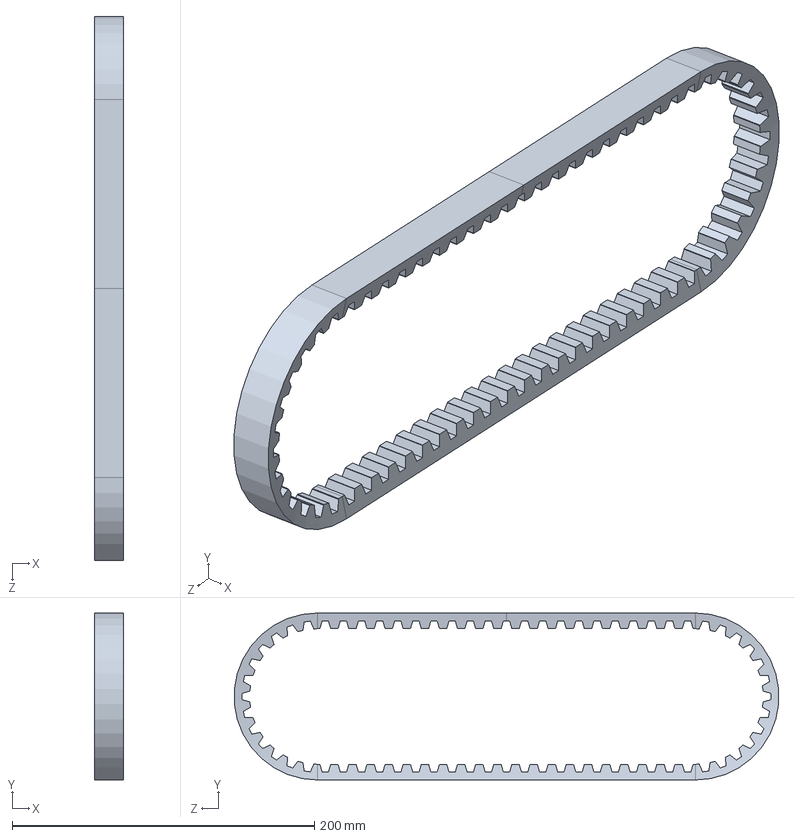
[picture p90: CAD file, 2020-09-12]
Mechanical/drivetrain/CVT/example-CVT/cinghia/cinghia.SLDPRT
19.0 x 110.5 x 360.0 mm
