AS-Wilson/RogueGP/Mechanical/drivetrain/CVT/example-CVT/Clutch-Bell/CLBPart2.SLDPRT

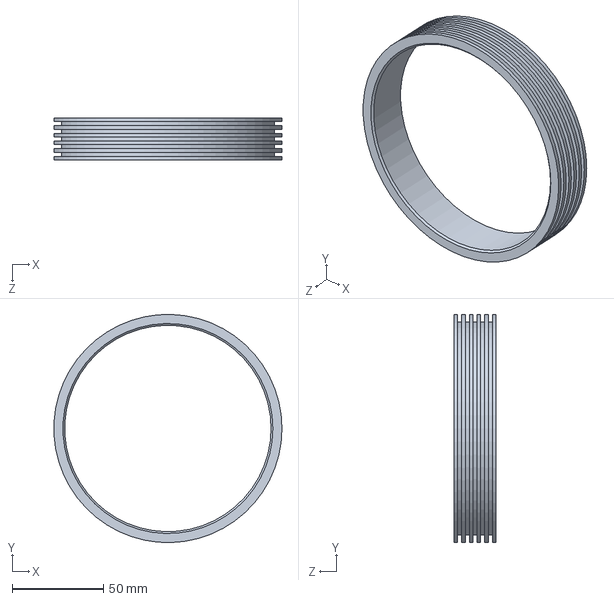
[picture p91: CAD file, 2020-09-12]
Mechanical/drivetrain/CVT/example-CVT/Clutch-Bell/CLBPart2.SLDPRT
124.9 x 124.9 x 23.0 mm
