AS-Wilson/RogueGP/Mechanical/drivetrain/CVT/example-CVT/MdC/TorsionController.SLDPRT

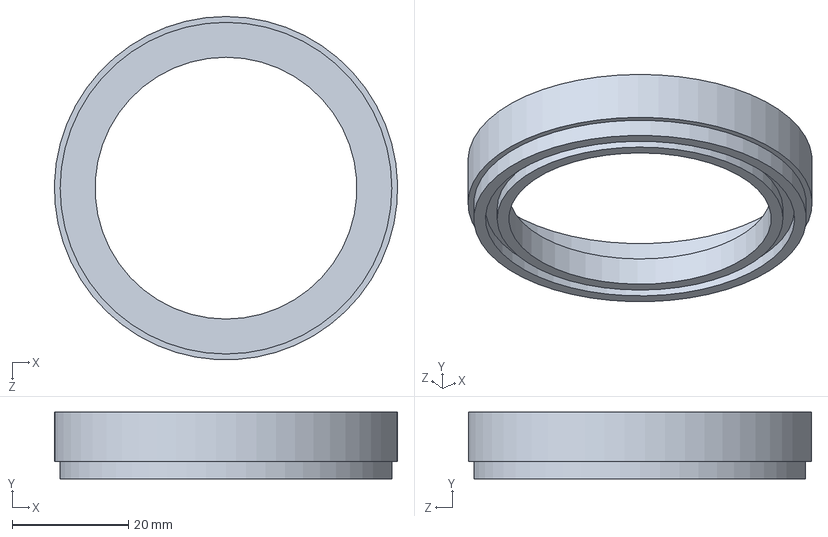
[picture p92: CAD file, 2020-09-12]
Mechanical/drivetrain/CVT/example-CVT/MdC/TorsionController.SLDPRT
59.0 x 11.5 x 58.9 mm
