AS-Wilson/RogueGP/Mechanical/drivetrain/CVT/example-CVT/Torque-Driver/TQParte1.SLDPRT

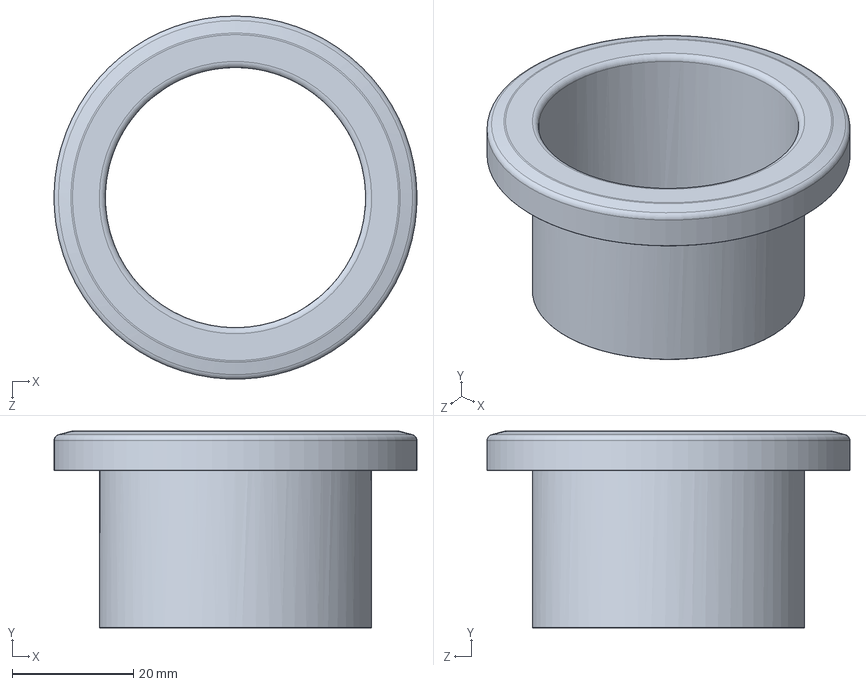
[picture p93: CAD file, 2020-09-12]
Mechanical/drivetrain/CVT/example-CVT/Torque-Driver/TQParte1.SLDPRT
60.0 x 32.5 x 60.0 mm
