AS-Wilson/RogueGP/Mechanical/drivetrain/CVT/example-CVT/Variator-multivar2000/moved half-pulley.SLDPRT

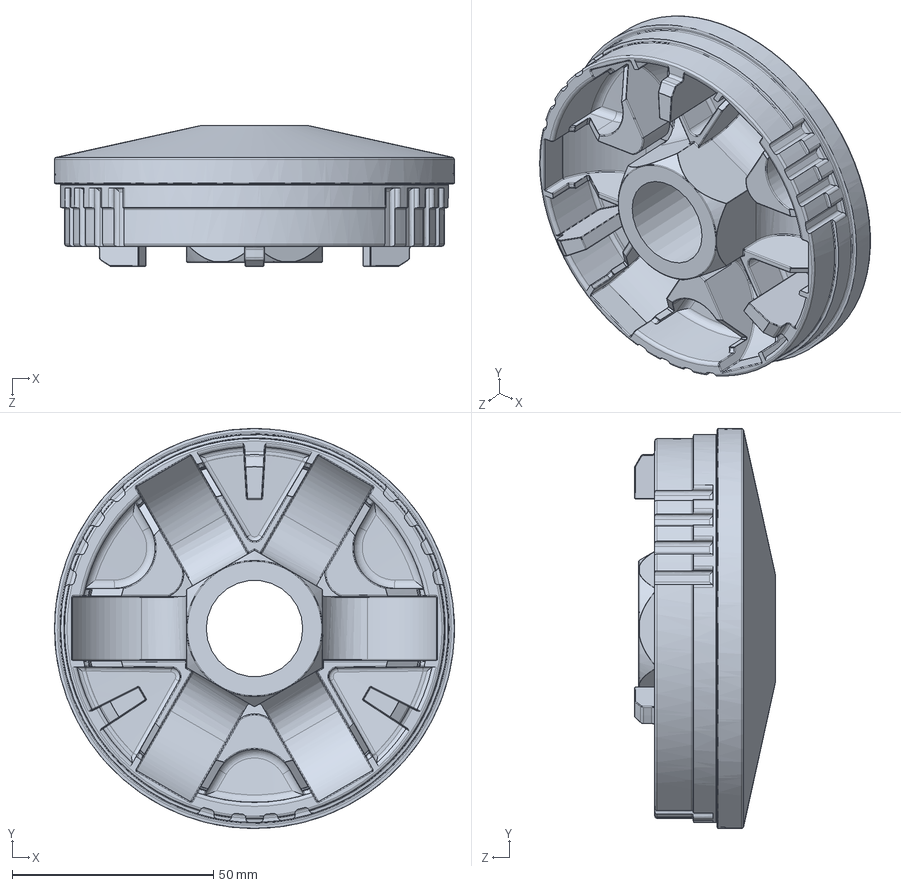
[picture p94: CAD file, 2020-09-12]
Mechanical/drivetrain/CVT/example-CVT/Variator-multivar2000/moved half-pulley.SLDPRT
99.5 x 99.5 x 35.0 mm
