AS-Wilson/RogueGP/Mechanical/drivetrain/CVT/example-CVT/ventilvar/VENParte31.SLDPRT

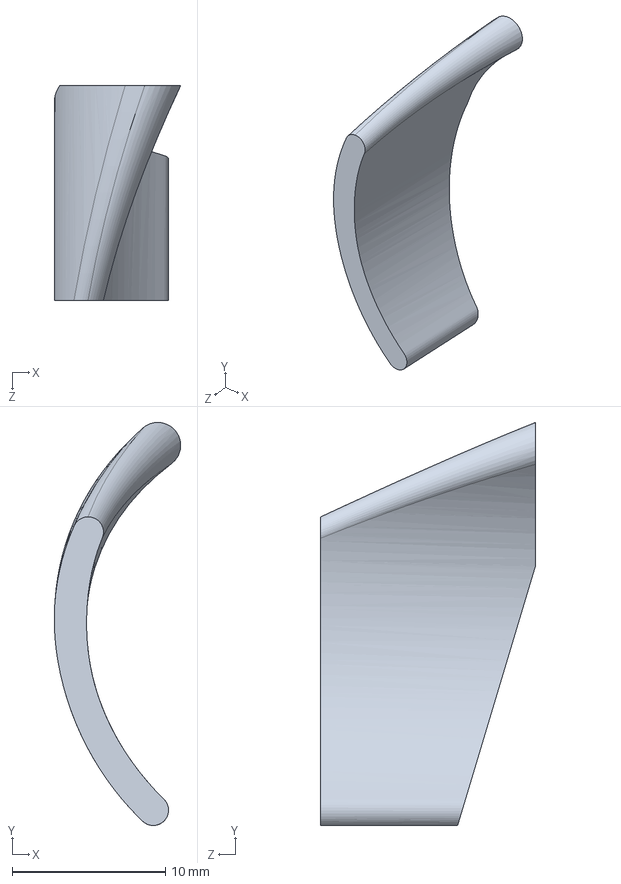
[picture p95: CAD file, 2020-09-12]
Mechanical/drivetrain/CVT/example-CVT/ventilvar/VENParte31.SLDPRT
8.24 x 26.3 x 14.0 mm
