AS-Wilson/RogueGP/Mechanical/standard-parts-&-example-designs/example-CVT/Clutch/CLpart7.SLDPRT

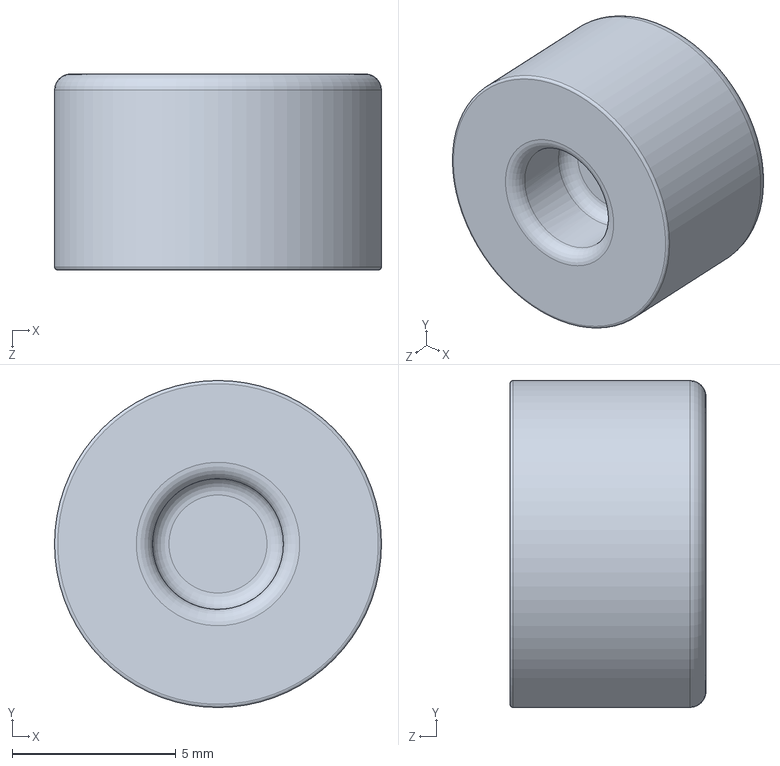
[picture p96: CAD file, 2020-09-12]
Mechanical/standard-parts-&-example-designs/example-CVT/Clutch/CLpart7.SLDPRT
10.0 x 10.0 x 6.00 mm
