AS-Wilson/RogueGP/Mechanical/standard-parts-&-example-designs/example-CVT/Torque-Driver/Parte3GR.SLDPRT

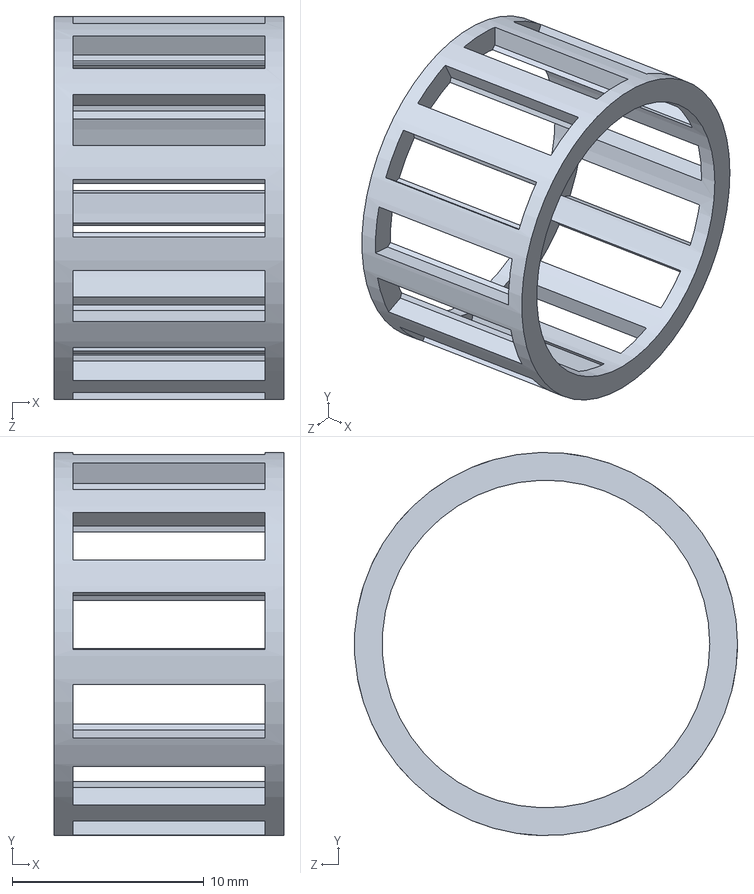
[picture p97: CAD file, 2020-09-12]
Mechanical/standard-parts-&-example-designs/example-CVT/Torque-Driver/Parte3GR.SLDPRT
12.0 x 20.0 x 20.0 mm
