AS-Wilson/RogueGP/Mechanical/standard-parts-&-example-designs/example-CVT/Variator-multivar2000/hub.SLDPRT

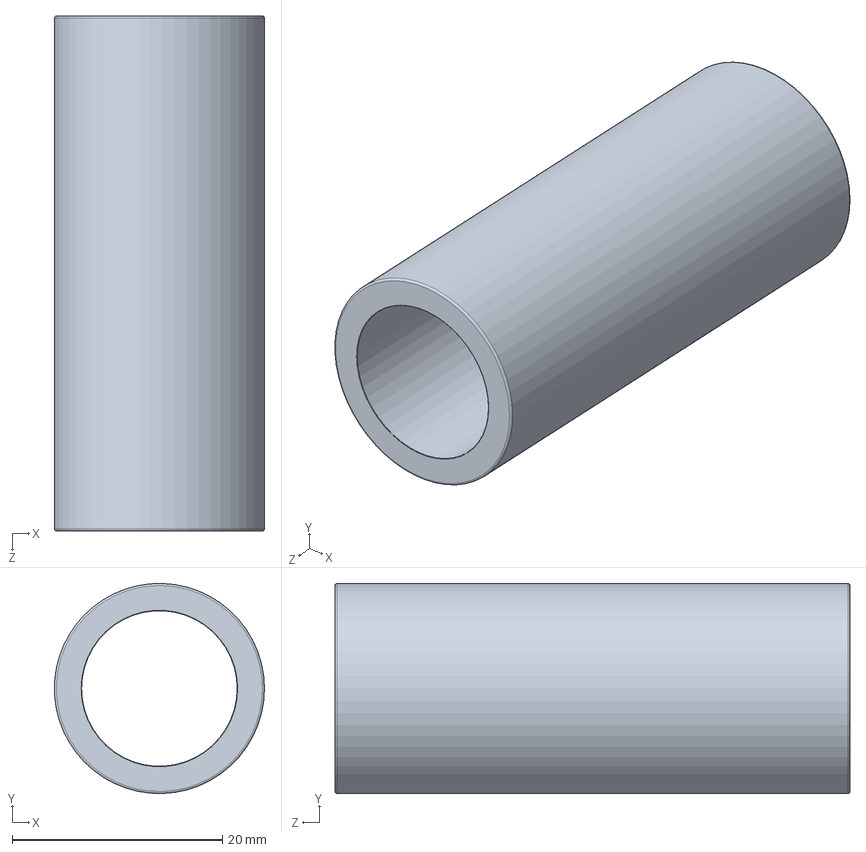
[picture p98: CAD file, 2020-09-12]
Mechanical/standard-parts-&-example-designs/example-CVT/Variator-multivar2000/hub.SLDPRT
20.0 x 20.0 x 49.0 mm
