AS-Wilson/RogueGP/Documentation/Part Drawings & Exports/Exports/roll-hoop-strut-knuckle-plain-coupler.stp

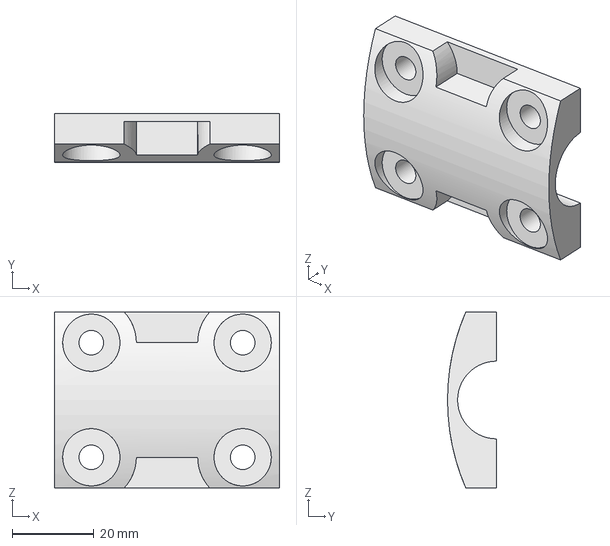
[picture p99: CAD file, 2020-09-22]
Documentation/Part Drawings & Exports/Exports/roll-hoop-strut-knuckle-plain-coupler.stp
55.0 x 12.0 x 43.0 mm
