AS-Wilson/RogueGP/Mechanical/drivetrain/CVT/example-CVT/Clutch/CLPart6.SLDPRT

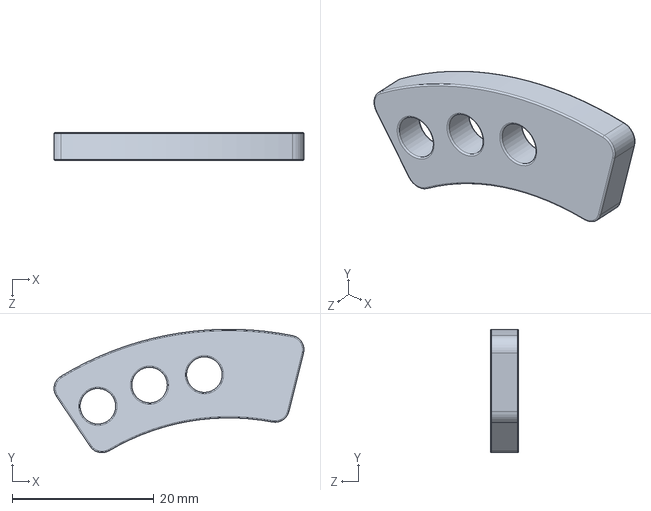
[picture p100: CAD file, 2020-09-12]
Mechanical/drivetrain/CVT/example-CVT/Clutch/CLPart6.SLDPRT
35.2 x 17.4 x 4.00 mm
