AS-Wilson/RogueGP/Mechanical/drivetrain/CVT/example-CVT/Torque-Driver/guarnizione2.SLDPRT

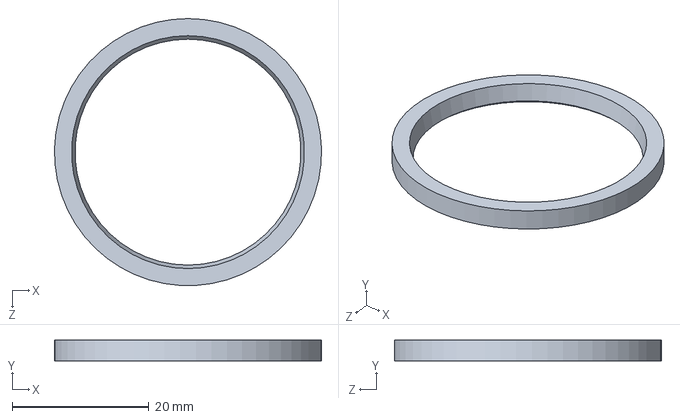
[picture p101: CAD file, 2020-09-12]
Mechanical/drivetrain/CVT/example-CVT/Torque-Driver/guarnizione2.SLDPRT
39.0 x 3.00 x 39.0 mm
