AS-Wilson/RogueGP/Mechanical/MB1000-chassis/roll-hoop/R720x100-roll-hoop/Exports/R720x100-roll-hoop.stp

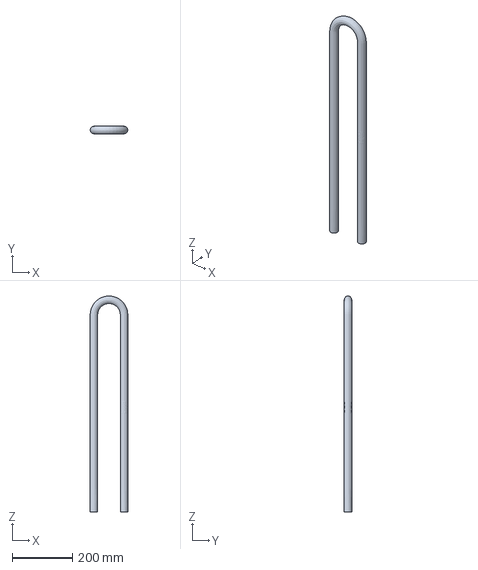
[picture p102: CAD file, 2020-09-17]
Mechanical/MB1000-chassis/roll-hoop/R720x100-roll-hoop/Exports/R720x100-roll-hoop.stp
125.0 x 25.0 x 717.5 mm
