AS-Wilson/RogueGP/Mechanical/standard-parts-&-example-designs/example-CVT/Clutch/frix1.SLDPRT

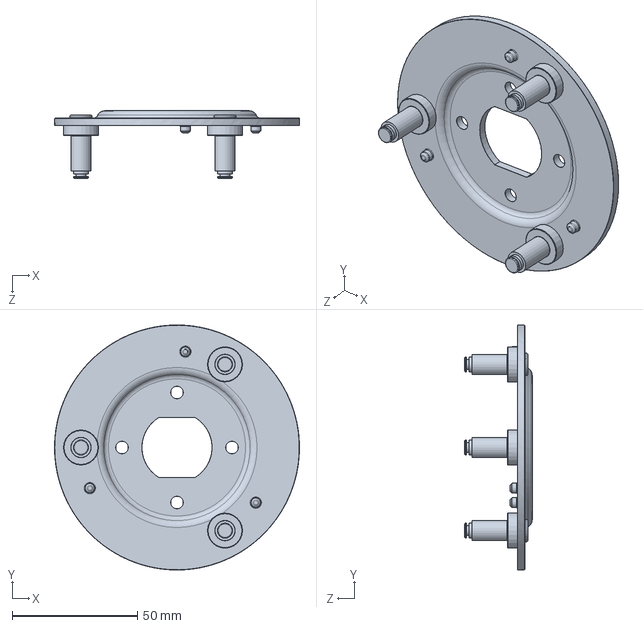
[picture p103: CAD file, 2020-09-12]
Mechanical/standard-parts-&-example-designs/example-CVT/Clutch/frix1.SLDPRT
98.0 x 98.0 x 27.0 mm
