AS-Wilson/RogueGP/Mechanical/standard-parts-&-example-designs/example-CVT/Torque-Driver/Parte1GR.SLDPRT

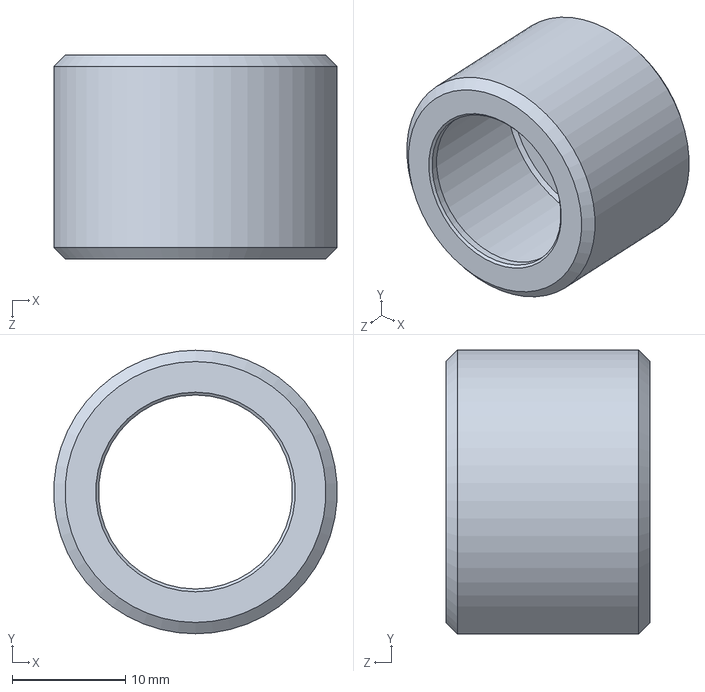
[picture p104: CAD file, 2020-09-12]
Mechanical/standard-parts-&-example-designs/example-CVT/Torque-Driver/Parte1GR.SLDPRT
25.0 x 25.0 x 18.0 mm
