AS-Wilson/RogueGP/Documentation/Part Drawings & Exports/Exports/roll-hoop-strut-knuckle.stp

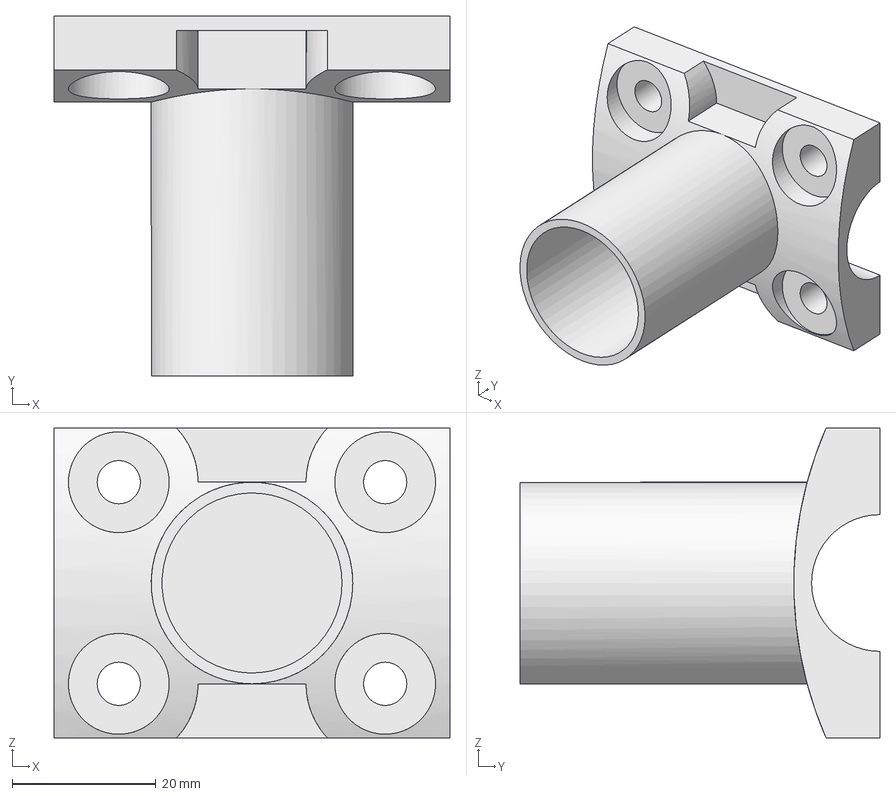
[picture p105: CAD file, 2020-09-22]
Documentation/Part Drawings & Exports/Exports/roll-hoop-strut-knuckle.stp
55.0 x 50.0 x 43.0 mm
