AS-Wilson/RogueGP/Mechanical/drivetrain/CVT/example-CVT/Clutch/coupling jaws.SLDPRT

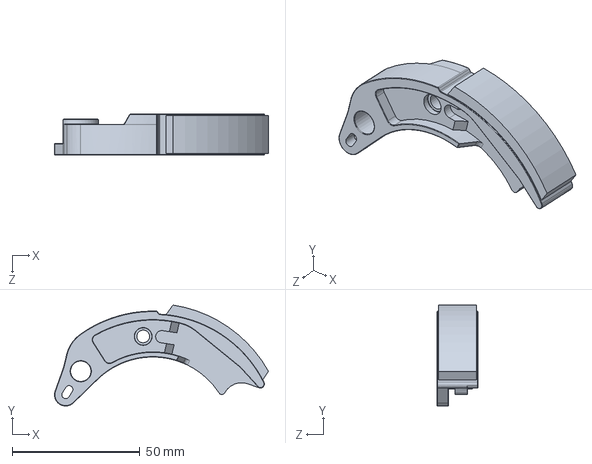
[picture p106: CAD file, 2020-09-12]
Mechanical/drivetrain/CVT/example-CVT/Clutch/coupling jaws.SLDPRT
83.9 x 39.6 x 16.0 mm
