AS-Wilson/RogueGP/Mechanical/drivetrain/CVT/example-CVT/Torque-Driver/TQParte7.SLDPRT

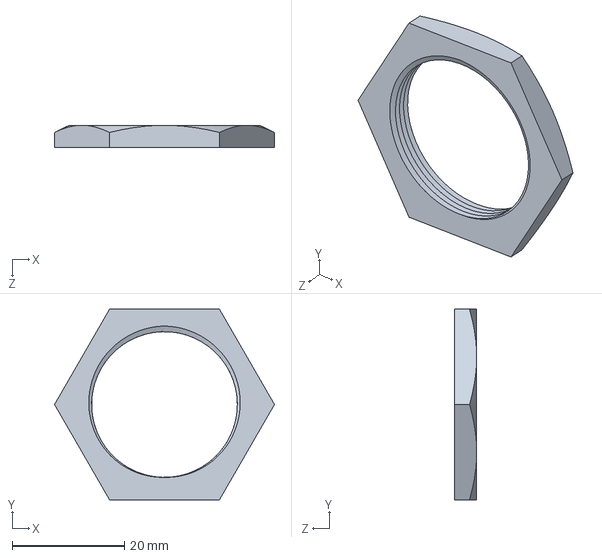
[picture p107: CAD file, 2020-09-12]
Mechanical/drivetrain/CVT/example-CVT/Torque-Driver/TQParte7.SLDPRT
39.3 x 34.0 x 4.00 mm
