AS-Wilson/RogueGP/Mechanical/drivetrain/CVT/example-CVT/Variator-multivar2000/slider.SLDPRT

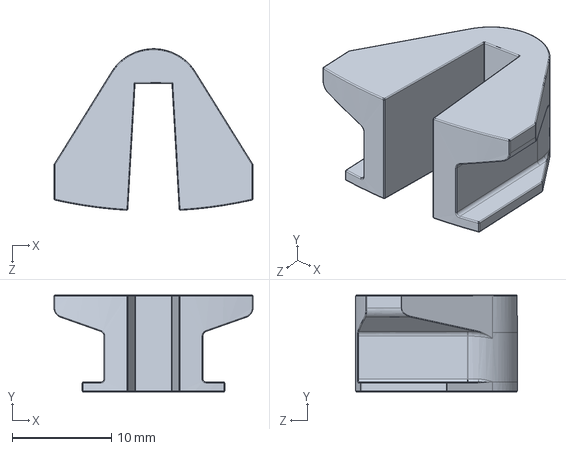
[picture p108: CAD file, 2020-09-12]
Mechanical/drivetrain/CVT/example-CVT/Variator-multivar2000/slider.SLDPRT
20.1 x 9.78 x 16.3 mm
