AS-Wilson/RogueGP/Mechanical/drivetrain/CVT/example-CVT/ventilvar/ventilvar.SLDPRT

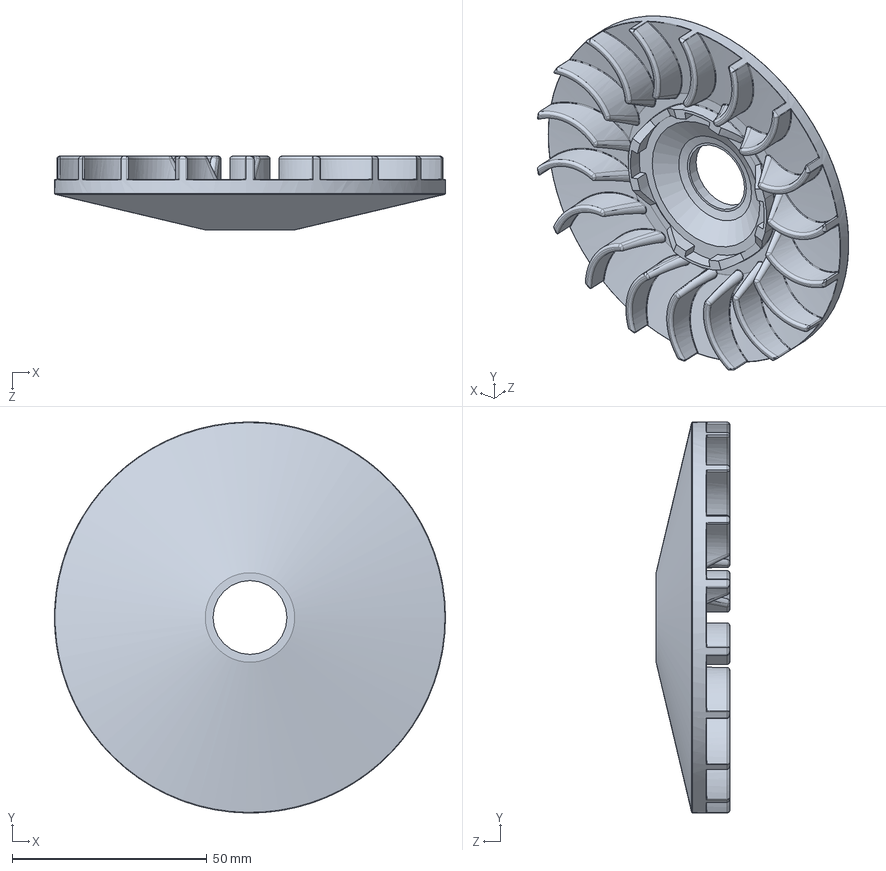
[picture p109: CAD file, 2020-09-12]
Mechanical/drivetrain/CVT/example-CVT/ventilvar/ventilvar.SLDPRT
100.5 x 100.5 x 19.0 mm
