AS-Wilson/RogueGP/Mechanical/MB1000-chassis/roll-hoop/R720x100-roll-hoop/Exports/R720x100-roll-hoop-bracing-strut.stp

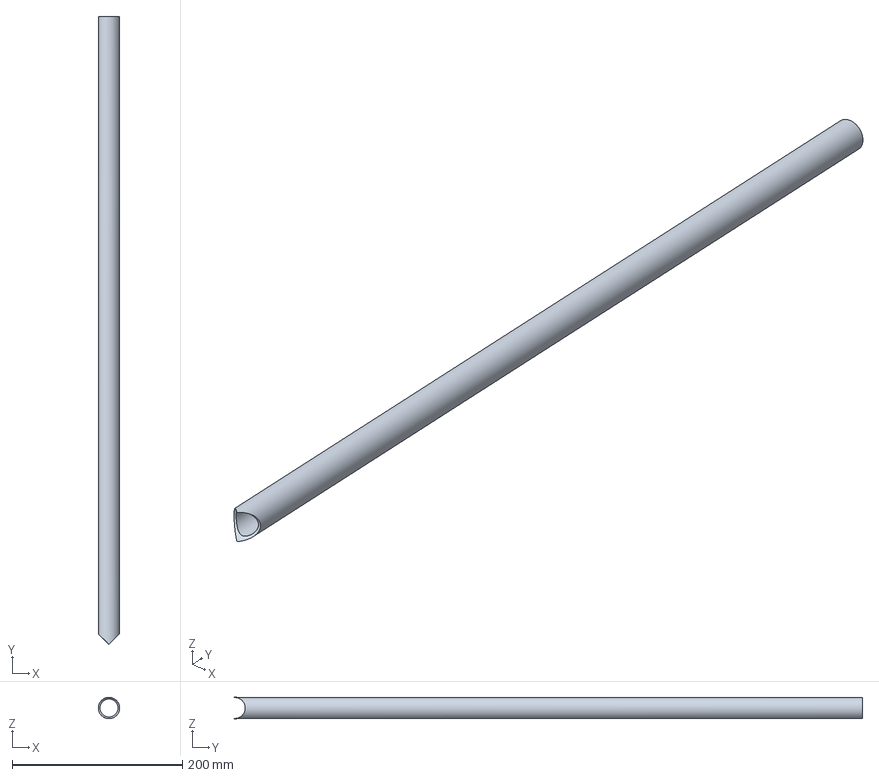
[picture p110: CAD file, 2020-09-17]
Mechanical/MB1000-chassis/roll-hoop/R720x100-roll-hoop/Exports/R720x100-roll-hoop-bracing-strut.stp
25.0 x 737.0 x 25.0 mm
