AS-Wilson/RogueGP/Documentation/Part Drawings & Exports/Exports/RH-axle.stp

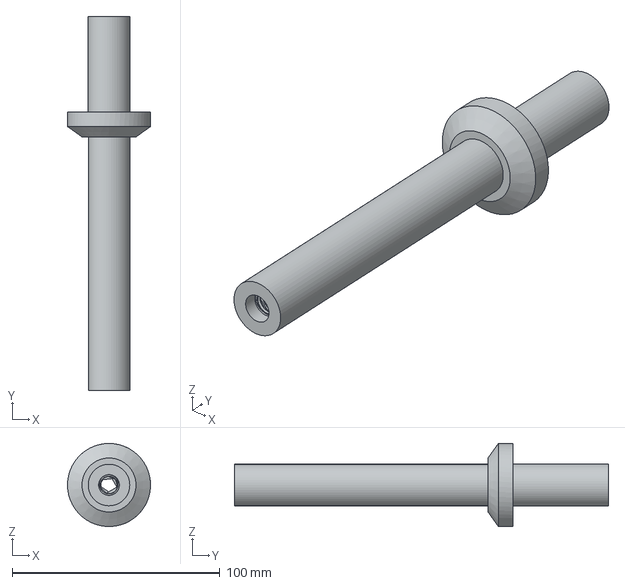
[picture p111: CAD file, 2020-09-22]
Documentation/Part Drawings & Exports/Exports/RH-axle.stp
40.0 x 180.0 x 40.0 mm
