AS-Wilson/RogueGP/Mechanical/drivetrain/CVT/example-CVT/Torque-Driver/Parte2GR.SLDPRT

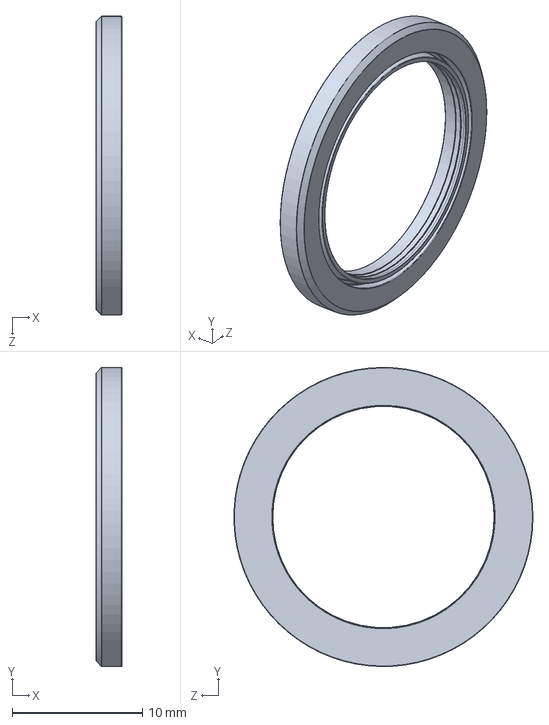
[picture p112: CAD file, 2020-09-12]
Mechanical/drivetrain/CVT/example-CVT/Torque-Driver/Parte2GR.SLDPRT
1.98 x 23.0 x 23.0 mm
