AS-Wilson/RogueGP/Mechanical/drivetrain/CVT/example-CVT/Variator-multivar2000/ventilvar.SLDPRT

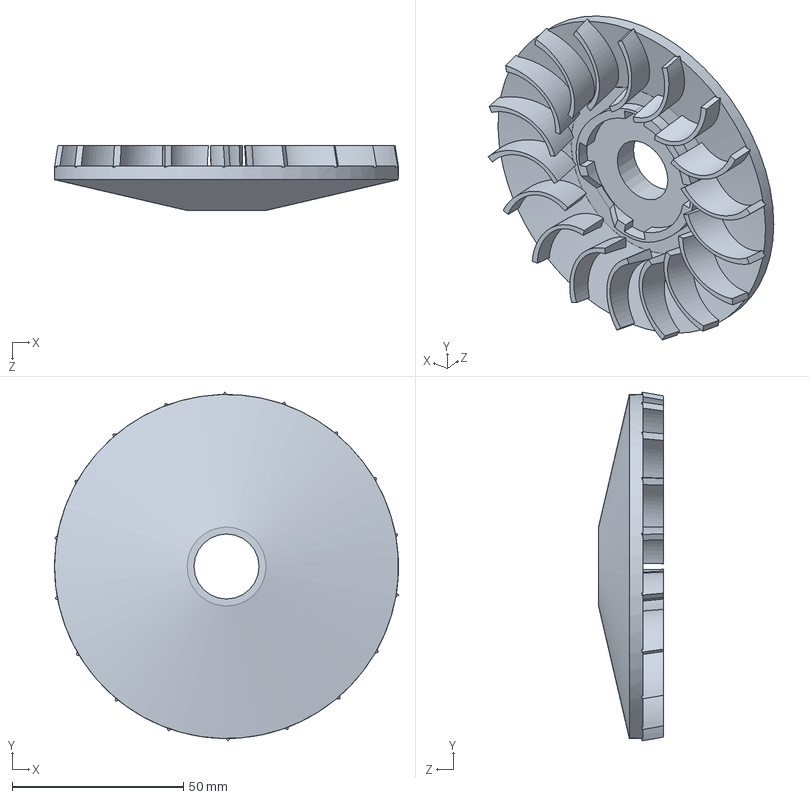
[picture p113: CAD file, 2020-09-12]
Mechanical/drivetrain/CVT/example-CVT/Variator-multivar2000/ventilvar.SLDPRT
100.5 x 101.9 x 19.0 mm
