AS-Wilson/RogueGP/Mechanical/MB1000-chassis/roll-hoop/R720x100-roll-hoop/Exports/R720x100-roll-hoop-cross-member.stp

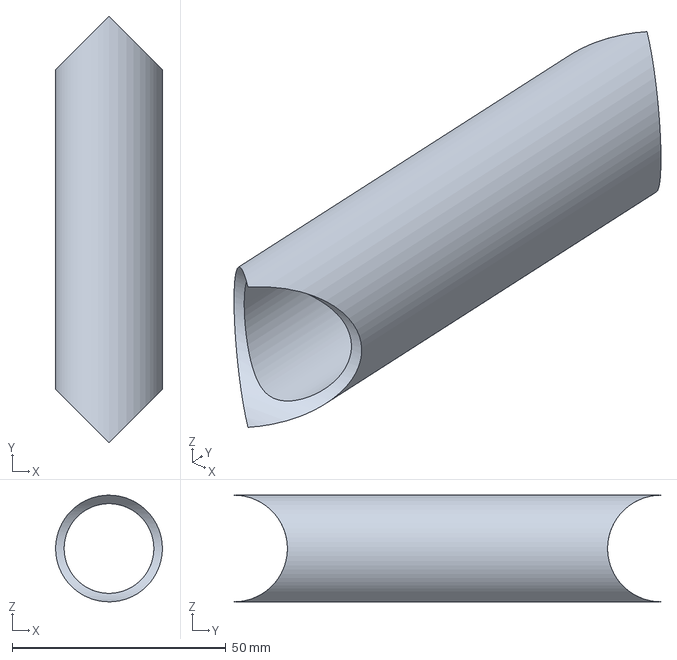
[picture p114: CAD file, 2020-09-17]
Mechanical/MB1000-chassis/roll-hoop/R720x100-roll-hoop/Exports/R720x100-roll-hoop-cross-member.stp
25.0 x 100.0 x 25.0 mm
