AS-Wilson/RogueGP/Mechanical/standard-parts-&-example-designs/example-CVT/Clutch/CLPart5.SLDPRT

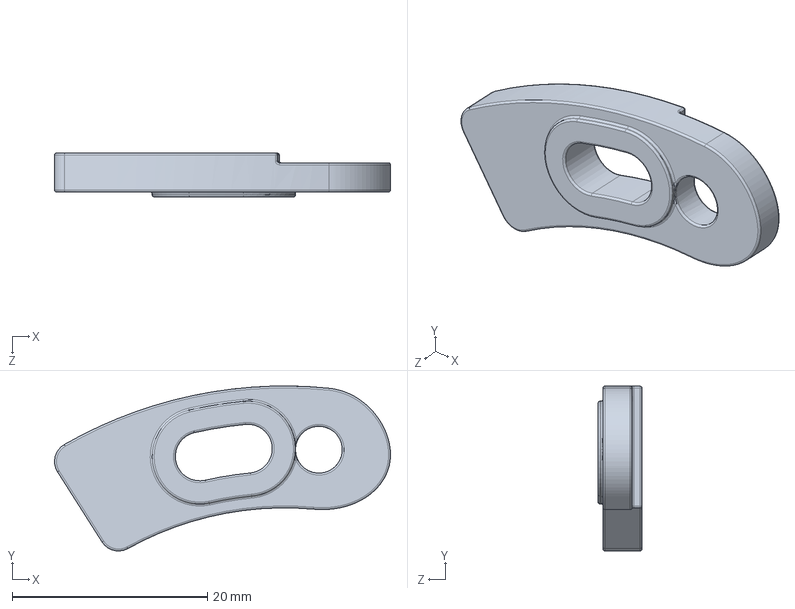
[picture p115: CAD file, 2020-09-12]
Mechanical/standard-parts-&-example-designs/example-CVT/Clutch/CLPart5.SLDPRT
34.5 x 16.9 x 4.50 mm
