AS-Wilson/RogueGP/Mechanical/drivetrain/CVT/example-CVT/Clutch/CLPart2.SLDPRT

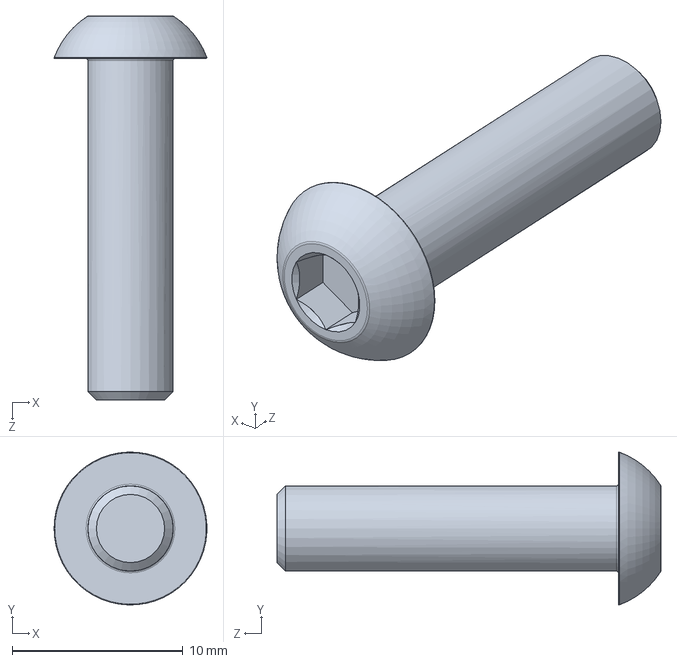
[picture p116: CAD file, 2020-09-12]
Mechanical/drivetrain/CVT/example-CVT/Clutch/CLPart2.SLDPRT
8.95 x 8.95 x 22.5 mm
