AS-Wilson/RogueGP/Mechanical/drivetrain/CVT/example-CVT/Variator-multivar2000/fixed cover.SLDPRT

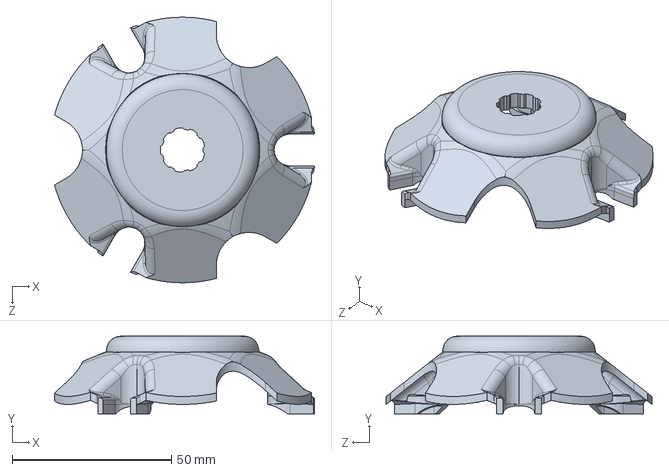
[picture p117: CAD file, 2020-09-12]
Mechanical/drivetrain/CVT/example-CVT/Variator-multivar2000/fixed cover.SLDPRT
81.7 x 24.5 x 83.5 mm
