AS-Wilson/RogueGP/Mechanical/standard-parts-&-example-designs/example-CVT/Torque-Driver/Parte2SM.SLDPRT

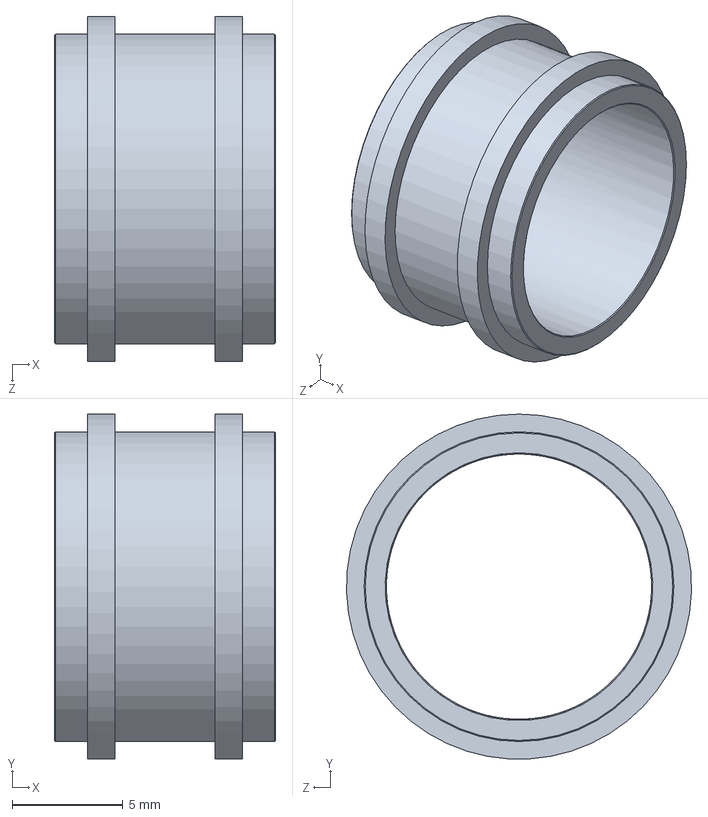
[picture p118: CAD file, 2020-09-12]
Mechanical/standard-parts-&-example-designs/example-CVT/Torque-Driver/Parte2SM.SLDPRT
10.0 x 15.6 x 15.6 mm
