AS-Wilson/RogueGP/Mechanical/drivetrain/CVT/example-CVT/Clutch/spring.SLDPRT

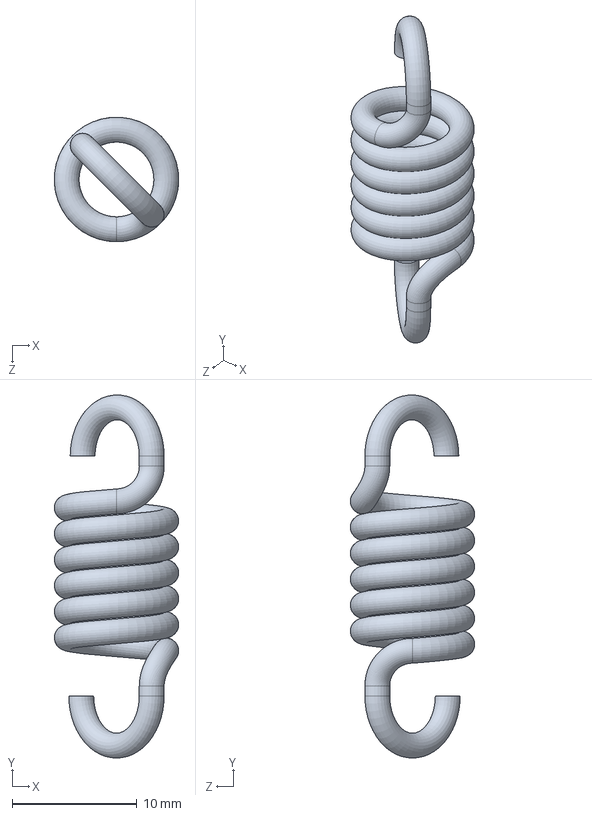
[picture p119: CAD file, 2020-09-12]
Mechanical/drivetrain/CVT/example-CVT/Clutch/spring.SLDPRT
10.00 x 29.2 x 10.00 mm
