AS-Wilson/RogueGP/Mechanical/standard-parts-&-example-designs/example-CVT/Variator-multivar2000/bushing.SLDPRT

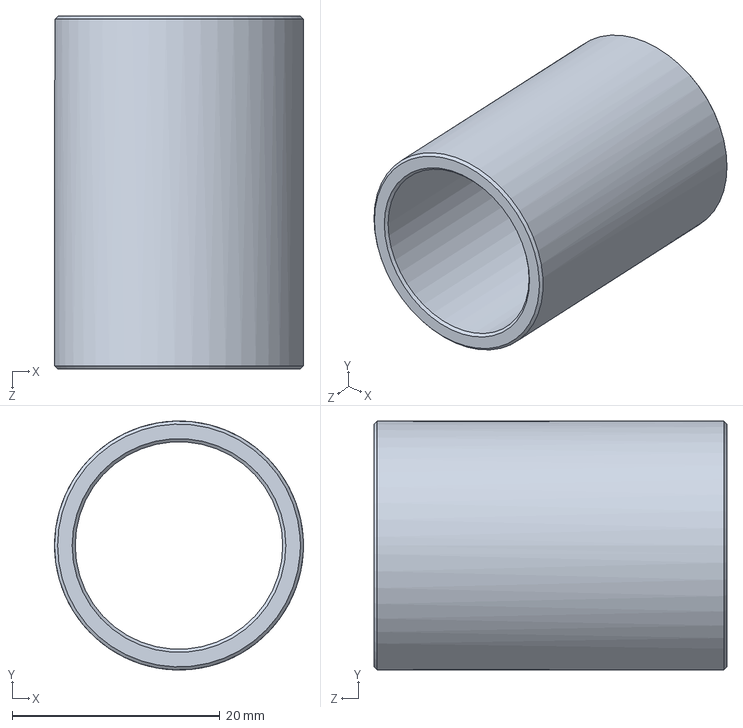
[picture p120: CAD file, 2020-09-12]
Mechanical/standard-parts-&-example-designs/example-CVT/Variator-multivar2000/bushing.SLDPRT
24.0 x 24.0 x 34.0 mm
