AS-Wilson/RogueGP/Mechanical/drivetrain/CVT/example-CVT/Torque-Driver/Parte4GR.SLDPRT

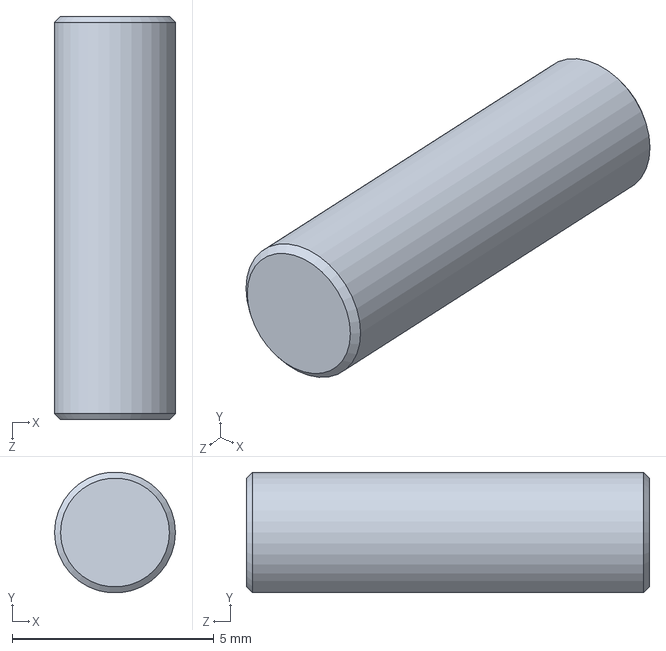
[picture p121: CAD file, 2020-09-12]
Mechanical/drivetrain/CVT/example-CVT/Torque-Driver/Parte4GR.SLDPRT
3.00 x 2.99 x 10.0 mm
