AS-Wilson/RogueGP/Mechanical/standard-parts-&-example-designs/example-CVT/Torque-Driver/TQParte2.SLDPRT

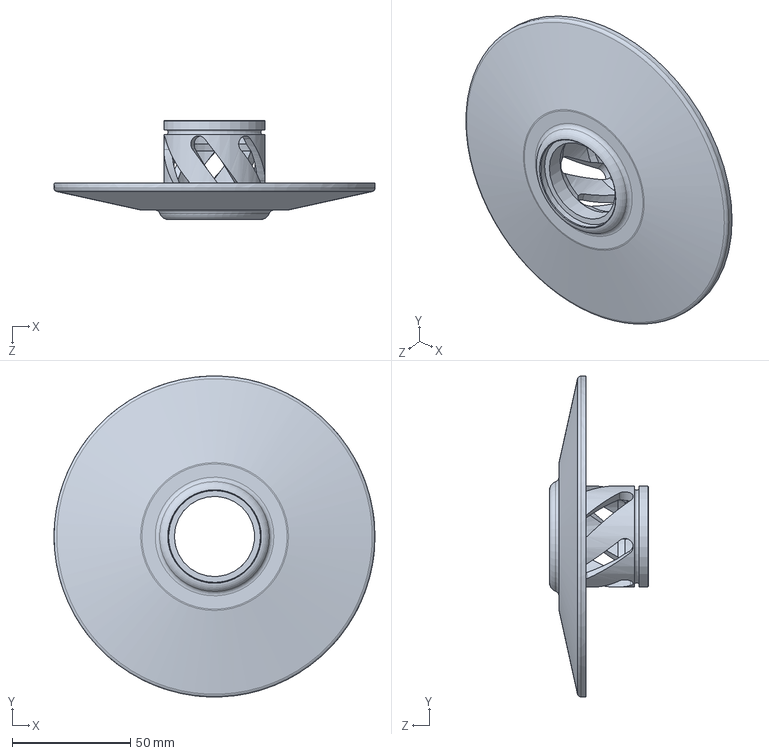
[picture p122: CAD file, 2020-09-12]
Mechanical/standard-parts-&-example-designs/example-CVT/Torque-Driver/TQParte2.SLDPRT
136.0 x 135.9 x 42.0 mm
