AS-Wilson/RogueGP/Mechanical/drivetrain/CVT/example-CVT/Clutch/seeger.SLDPRT

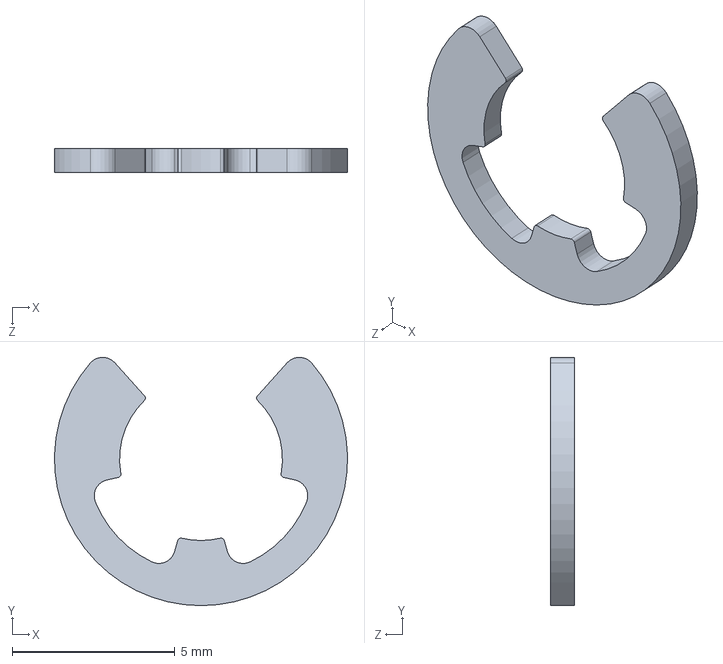
[picture p123: CAD file, 2020-09-12]
Mechanical/drivetrain/CVT/example-CVT/Clutch/seeger.SLDPRT
9.00 x 7.62 x 0.75 mm
