AS-Wilson/RogueGP/Mechanical/drivetrain/CVT/example-CVT/Torque-Driver/guarnizione.SLDPRT

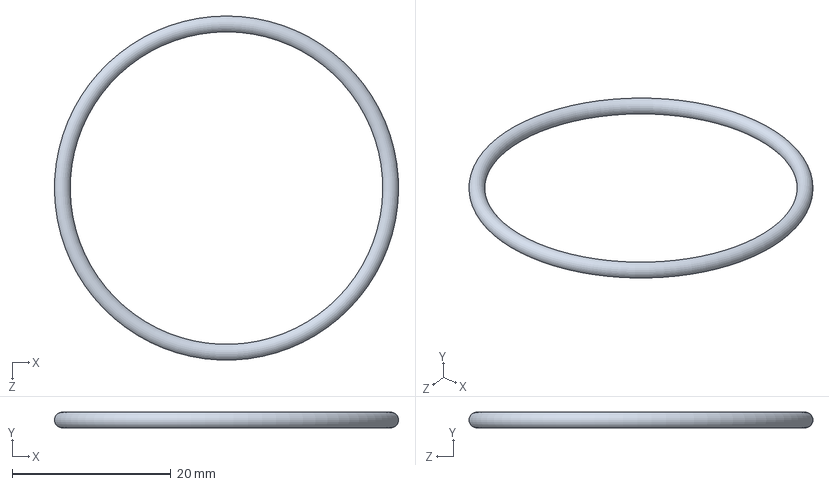
[picture p124: CAD file, 2020-09-12]
Mechanical/drivetrain/CVT/example-CVT/Torque-Driver/guarnizione.SLDPRT
43.4 x 2.00 x 43.4 mm
