AS-Wilson/RogueGP/Mechanical/standard-parts-&-example-designs/example-CVT/Clutch/CLPart4.SLDPRT

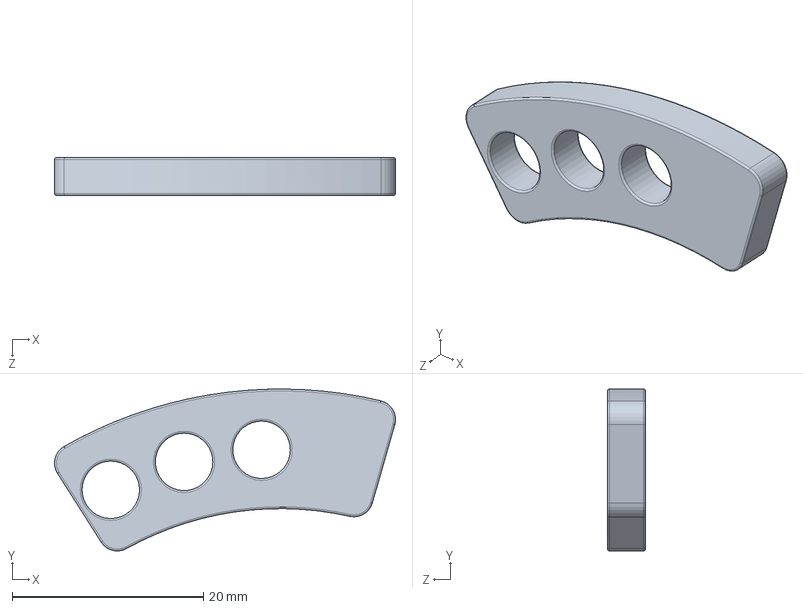
[picture p125: CAD file, 2020-09-12]
Mechanical/standard-parts-&-example-designs/example-CVT/Clutch/CLPart4.SLDPRT
35.6 x 16.9 x 4.00 mm
