AS-Wilson/RogueGP/Mechanical/standard-parts-&-example-designs/example-CVT/Torque-Driver/Parte3SM.SLDPRT

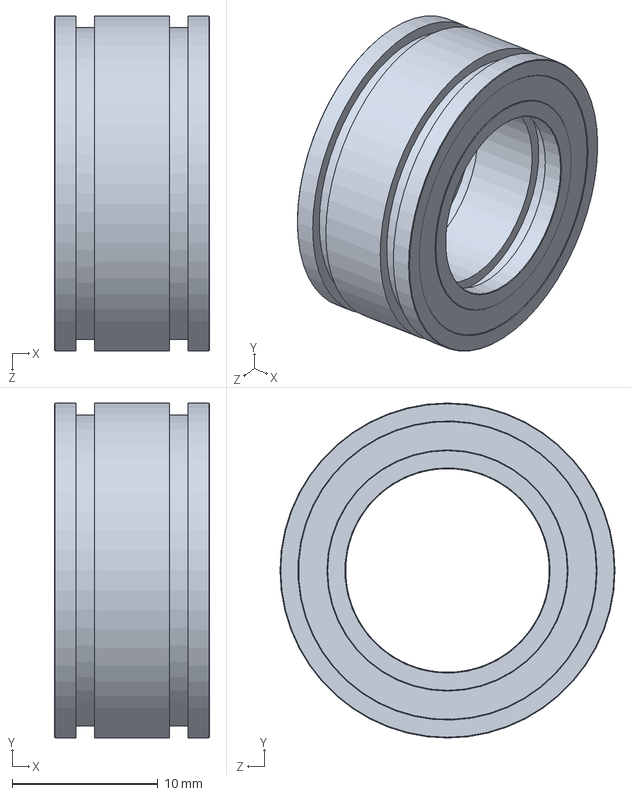
[picture p126: CAD file, 2020-09-12]
Mechanical/standard-parts-&-example-designs/example-CVT/Torque-Driver/Parte3SM.SLDPRT
10.7 x 23.0 x 23.0 mm
