AS-Wilson/RogueGP/Mechanical/drivetrain/CVT/example-CVT/Torque-Driver/TQParte4.SLDPRT

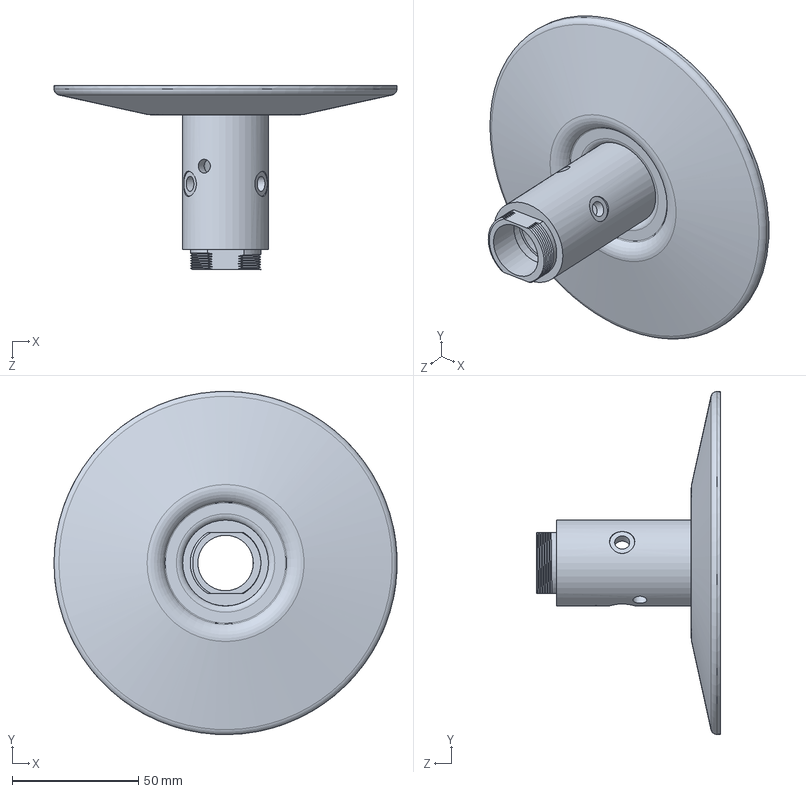
[picture p127: CAD file, 2020-09-12]
Mechanical/drivetrain/CVT/example-CVT/Torque-Driver/TQParte4.SLDPRT
135.9 x 136.0 x 73.0 mm
