AS-Wilson/RogueGP/Mechanical/standard-parts-&-example-designs/example-CVT/Torque-Driver/Parte1SM.SLDPRT

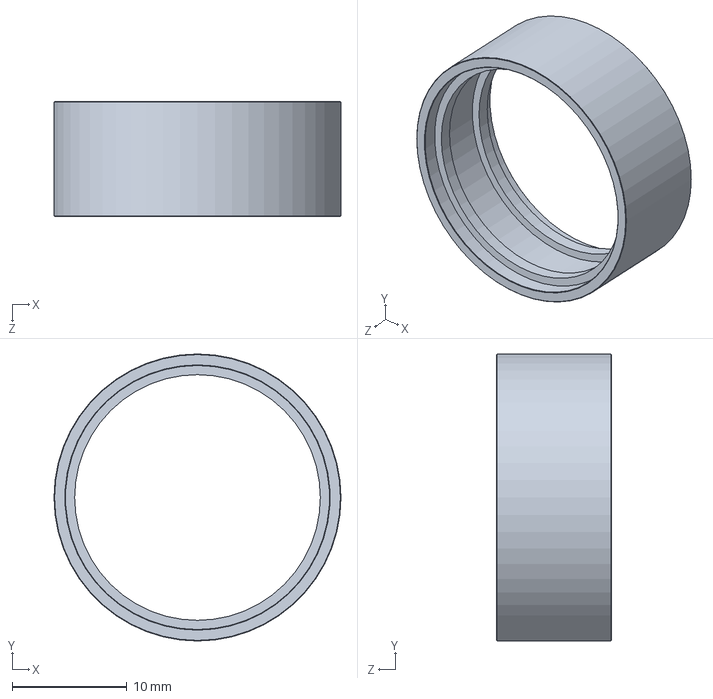
[picture p128: CAD file, 2020-09-12]
Mechanical/standard-parts-&-example-designs/example-CVT/Torque-Driver/Parte1SM.SLDPRT
25.0 x 25.0 x 10.0 mm
