AS-Wilson/RogueGP/Documentation/Porfolio/Renders/Steering build 1.jpg

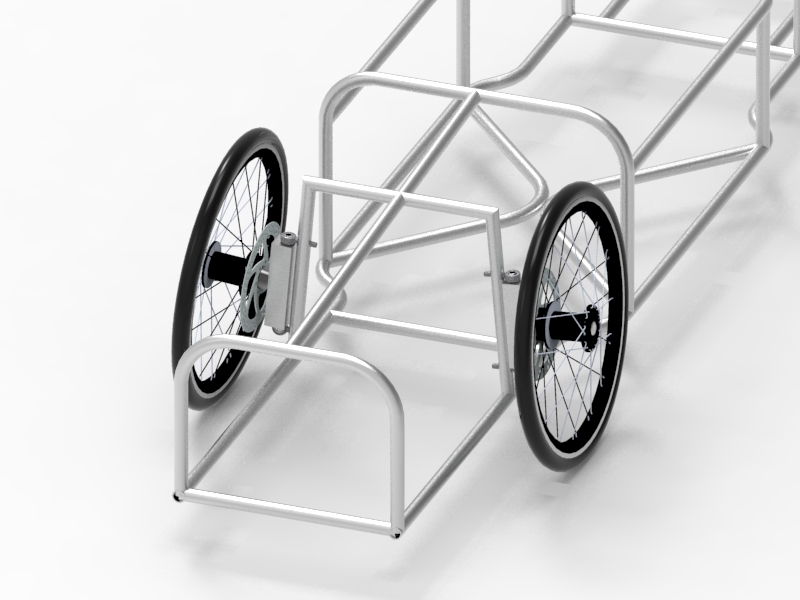
Documentation/Porfolio/Renders/Steering build 1.jpg
