AS-Wilson/RogueGP/Documentation/Porfolio/Renders/Steering build 3 img1.jpg

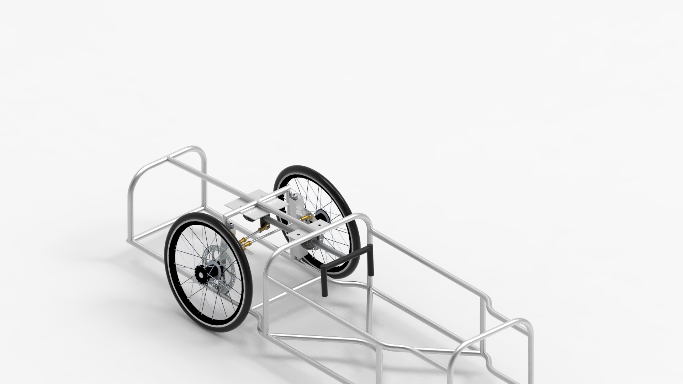
Documentation/Porfolio/Renders/Steering build 3 img1.jpg
