AS-Wilson/RogueGP/Documentation/Porfolio/Renders/Steering build 3 img 2.jpg

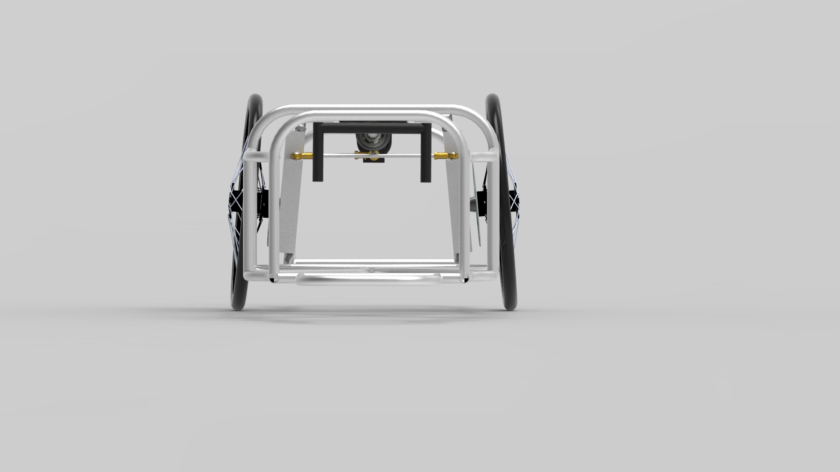
Documentation/Porfolio/Renders/Steering build 3 img 2.jpg
