AS-Wilson/RogueGP/Documentation/Porfolio/Renders/Steering build 5.jpg

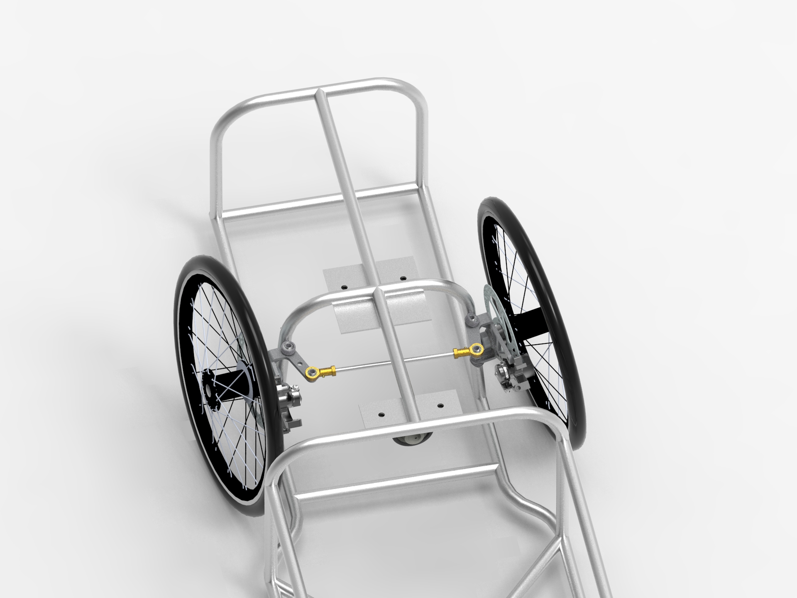
Documentation/Porfolio/Renders/Steering build 5.jpg
