AS-Wilson/RogueGP/Documentation/Porfolio/Renders/Steering wheel build 1.jpg

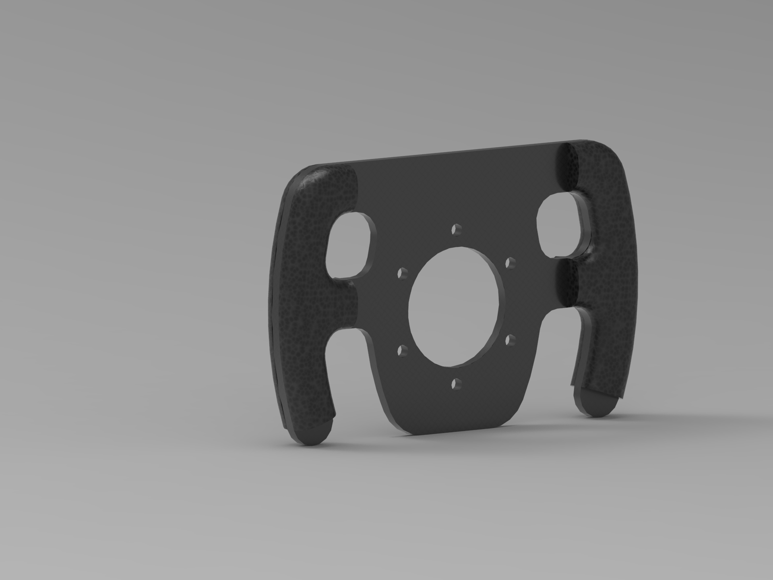
Documentation/Porfolio/Renders/Steering wheel build 1.jpg
