AS-Wilson/RogueGP/Electrical&Electronic/Common Controller Setup.png

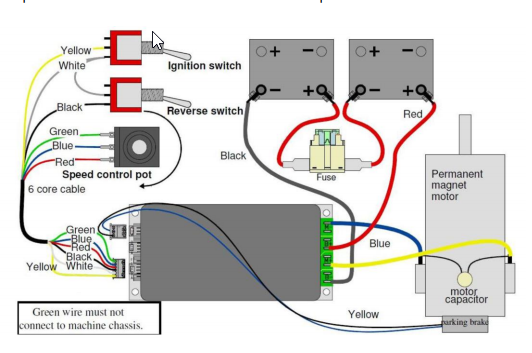
Electrical&Electronic/Common Controller Setup.png
