AS-Wilson/RogueGP/Documentation/Porfolio/Renders/Green metallic test.jpg

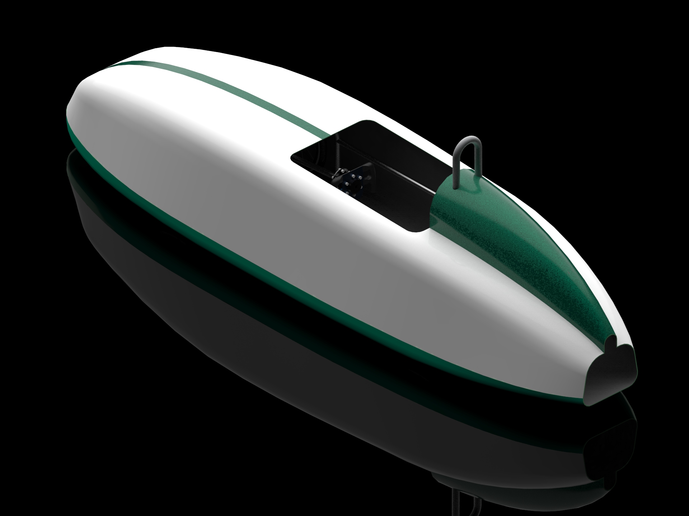
Documentation/Porfolio/Renders/Green metallic test.jpg
