AS-Wilson/RogueGP/Documentation/Part Drawings & Exports/Drawings/2020-heat-sink-drawing.pdf

1 | 2 | 3 | 4 | 5 | 6 | 7 | 8 | 9 | 10 | 11 | 12

A

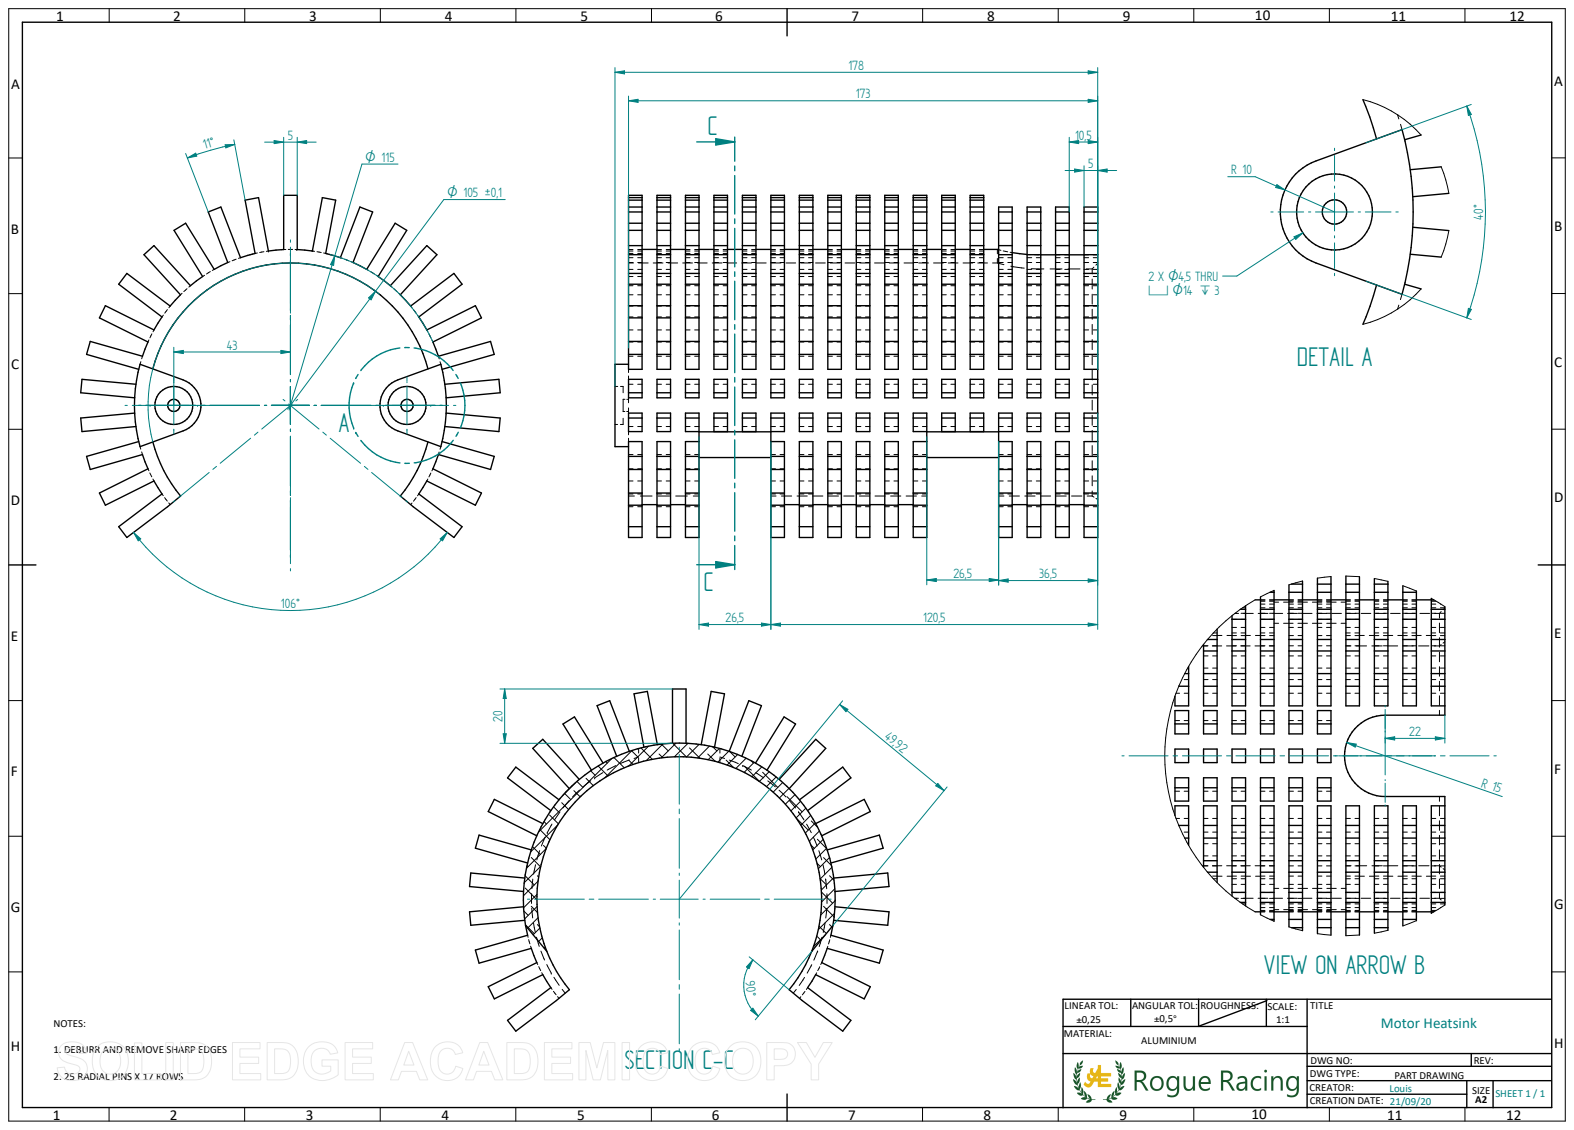
[picture p139: page 1]
SHEET 1 / 1 Louis 21/09/20; TITLE; Motor Heatsink; DWG NO:; REV:; SIZE A2; LINEAR TOL:; ANGULAR TOL: ROUGHNESS:; MATERIAL:; SCALE:; DWG TYPE: CREATOR: CREATION DATE:; DETAIL A; 2 X O4,5 THRU c O14 ` 3; SECTION C-C; NOTES:; ALUMINIUM; PART DRAWING

VIEW ON ARROW B

1. DEBURR AND REMOVE SHARP EDGES

2. 25 RADIAL PINS X 17 ROWS
