AS-Wilson/RogueGP/Documentation/Part Drawings & Exports/Drawings/LH-axle.pdf

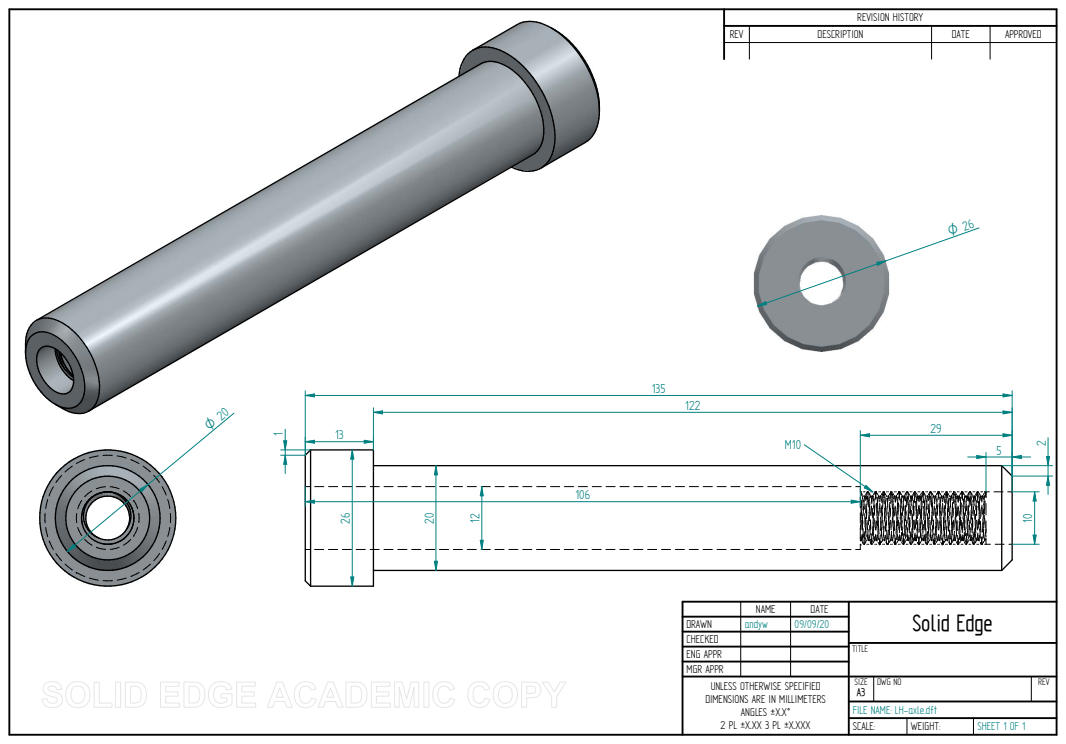
[picture p140: page 1]
TITLE; SCALE:; WEIGHT:; SHEET 1 OF 1

REVISION HISTORY

REV | DESCRIPTION | DATE | APPROVED

NAME | DATE | Solid Edge

DRAWN | andyw | 09/09/20
CHECKED
ENG APPR
MGR APPR
UNLESS OTHERWISE SPECIFIED DIMENSIONS ARE IN MILLIMETERS ANGLES ±X.X° 2 PL ±X.XX 3 PL ±X.XXX | SIZE A3 | DWG NO | REV

FILE NAME: LH-axle.dft
