AS-Wilson/RogueGP/Documentation/Part Drawings & Exports/Drawings/RH-axle-spacer-drawing.pdf

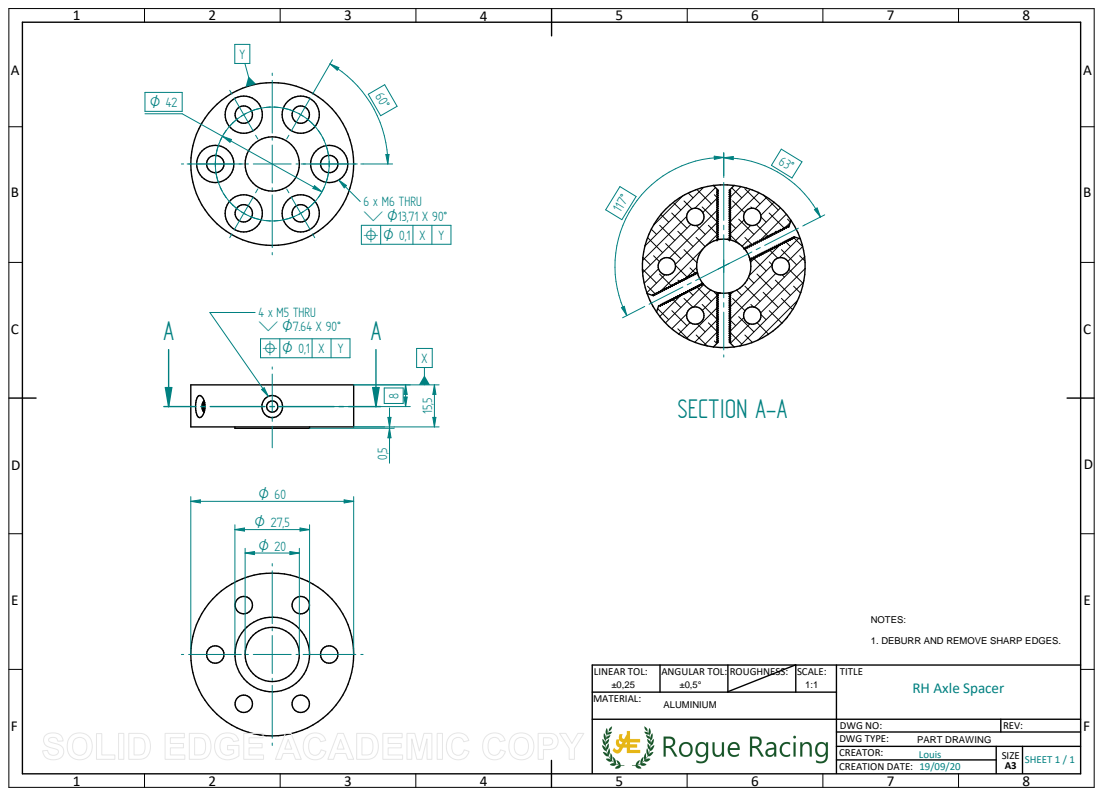
[picture p141: page 1]
SHEET 1 / 1 Louis 19/09/20; TITLE; DWG NO:; REV:; SIZE A3; LINEAR TOL:; ANGULAR TOL: ROUGHNESS:; MATERIAL:; SCALE:; DWG TYPE: CREATOR: CREATION DATE:; ALUMINIUM; PART DRAWING; SECTION A-A; 4 x M5 THRU s O7.64 X 90v; 6 x M6 THRU s O13,71 X 90°; NOTES:

1. DEBURR AND REMOVE SHARP EDGES.

RH Axle Spacer
