AS-Wilson/RogueGP/Documentation/Part Drawings & Exports/Drawings/roll-hoop-strut-knuckle-drawing.pdf

1 | 2 | 3 | 4 | 5 | 6 | 7 | 8

B

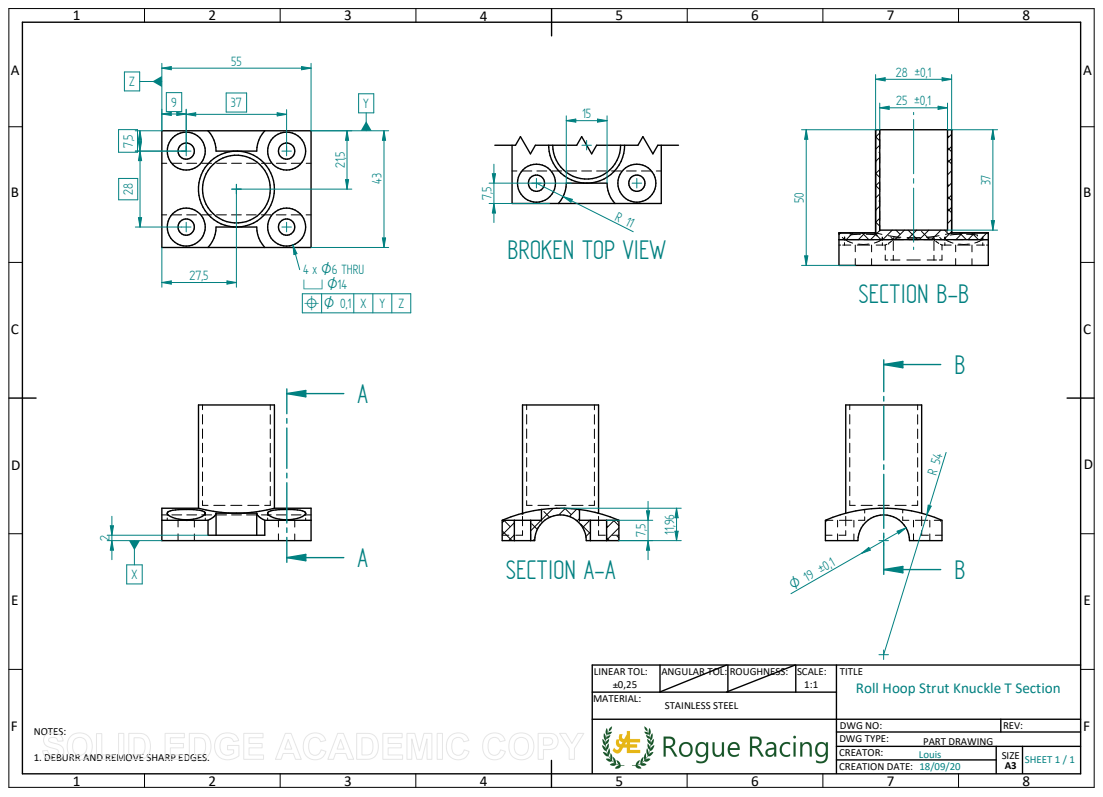
[picture p142: page 1]
SHEET 1 / 1 Louis 18/09/20; DWG NO:; REV:; SIZE A3; LINEAR TOL:; ANGULAR TOL: ROUGHNESS:; MATERIAL:; SCALE:; DWG TYPE: CREATOR: CREATION DATE:; SECTION B-B; SECTION A-A; STAINLESS STEEL; 4 x O6 THRU c O14; PART DRAWING; NOTES:

BROKEN TOP VIEW

TITLE
Roll Hoop Strut Knuckle T Section

1. DEBURR AND REMOVE SHARP EDGES.
