AS-Wilson/RogueGP/Documentation/Part Drawings & Exports/Drawings/roll-hoop-strut-knuckle-plain-coupler-drawing.pdf

1 | 2 | 3 | 4 | 5 | 6 | 7 | 8

B

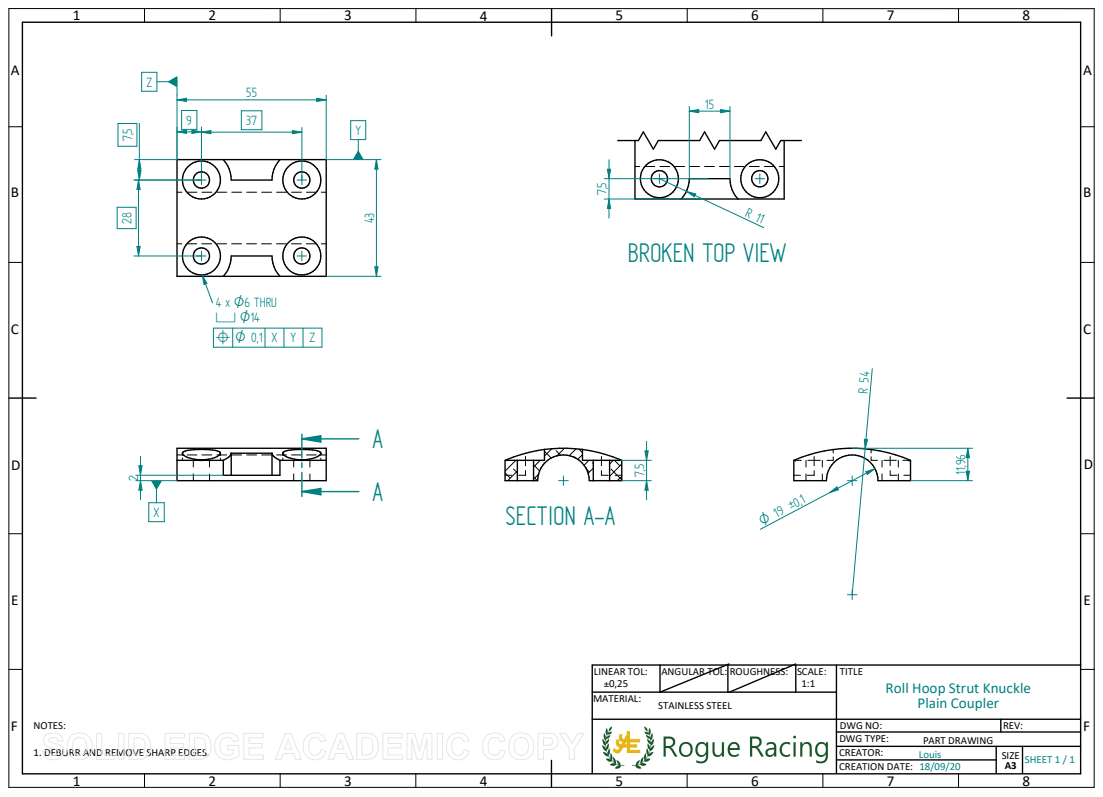
[picture p143: page 1]
SHEET 1 / 1 Louis 18/09/20; DWG NO:; REV:; SIZE A3; LINEAR TOL:; ANGULAR TOL: ROUGHNESS:; MATERIAL:; SCALE:; DWG TYPE: CREATOR: CREATION DATE:; STAINLESS STEEL; PART DRAWING; 4 x O6 THRU c O14; SECTION A-A; NOTES:

BROKEN TOP VIEW

TITLE
Roll Hoop Strut Knuckle
Plain Coupler

1. DEBURR AND REMOVE SHARP EDGES.
