AS-Wilson/RogueGP/Documentation/Part Drawings & Exports/Drawings/roll-hoop-u-bolt-saddle.pdf

1 | 2 | 3 | 4 | 5 | 6

A

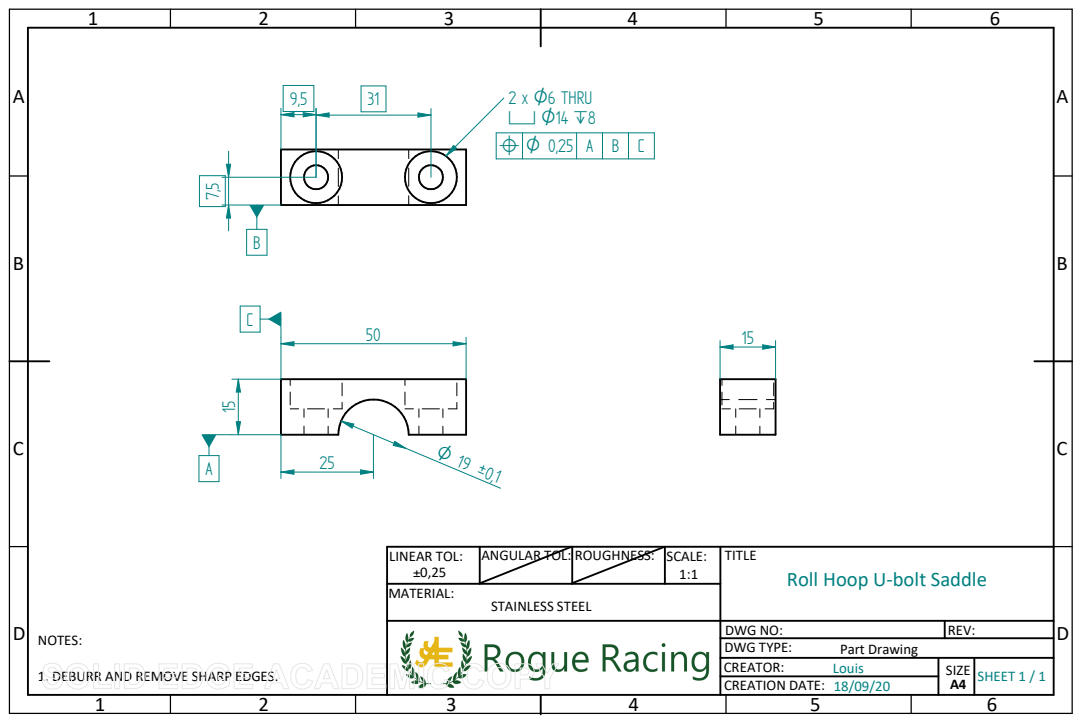
[picture p144: page 1]
SHEET 1 / 1 Louis 18/09/20; DWG NO:; REV:; SIZE A4; LINEAR TOL:; ANGULAR TOL: ROUGHNESS:; MATERIAL:; SCALE:; DWG TYPE: CREATOR: CREATION DATE:; O6 THRU c; Part Drawing; NOTES:; STAINLESS STEEL

TITLE
Roll Hoop U-bolt Saddle

1. DEBURR AND REMOVE SHARP EDGES.
