AS-Wilson/RogueGP/Documentation/Part Drawings & Exports/Drawings/upright-spacer-drawing.pdf

1 | 2 | 3 | 4 | 5 | 6

A

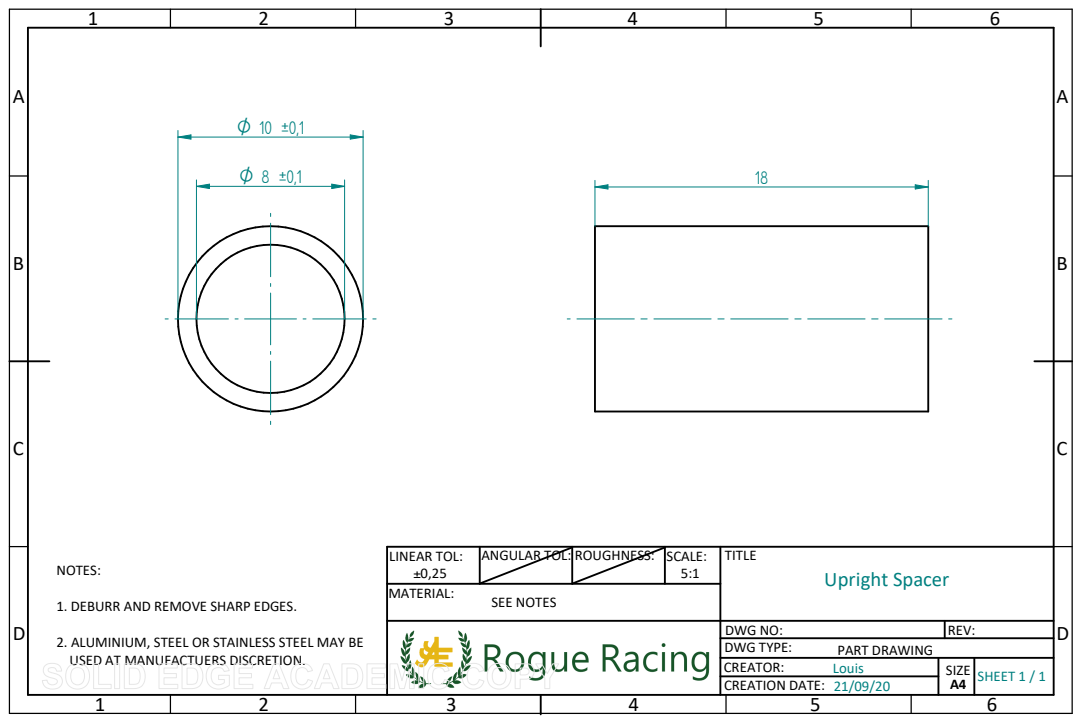
[picture p145: page 1]
SHEET 1 / 1 Louis 21/09/20; TITLE; Upright Spacer; DWG NO:; REV:; SIZE A4; LINEAR TOL:; ANGULAR TOL: ROUGHNESS:; MATERIAL:; SCALE:; DWG TYPE: CREATOR: CREATION DATE:; PART DRAWING; NOTES:; SEE NOTES

1. DEBURR AND REMOVE SHARP EDGES.
2. ALUMINIUM, STEEL OR STAINLESS STEEL MAY BE
USED AT MANUFACTUERS DISCRETION.
